Daxxn/LightDrum/Docs/Calculations/PowerConsumption.ods

Sheet: Power Rails
Power Rails
Name | Voltage | Current
+12V | 12 | 0
Vdrive | 12 | 16
VCC | 5 | 0.003
VDD | 3.3 | 0.4421
VAA | 3.3 | 0.014
VDDA | 3.3 | 0
Name | Input | Part # | Output | Current MAX
VCC | 12 | LM22673-5V | 5 | 3
VDD | 5 | AP3401 | 3.3 | 1
VAA | 5 | TPS7A94 | 3.3 | 1
VDDA | 3.3 | Filter | 3.3 | 0.5

Sheet: Consumption
Power Consumption
+12V | Total: | 0 | VCC | Total: | 0.003 | VDD | Total: | 0.4421 | VAA | Total: | 0.014 | VDDA | Total: | 0 | Typical Resistance Draw
Part # | Source | Current | Part # | Source | Current | Part # | Source | Current | Part # | Source | Current | Part # | Source | Current | 20k | 0.000165
 |  |  | SLG55021 | 5 | 0.003 | STM32F412VET3 | 3.3 | 0.16 | PCM1821 | 3.3 | 0.014
 |  |  |  |  |  | PCM1821 | 3.3 | 0.0001
 |  |  |  |  |  | PCA9634 | 3.3 | 0.01
 |  |  |  |  |  | PCA9634 | 3.3 | 0.01
 |  |  |  |  |  | PCA9634 | 3.3 | 0.01
 |  |  |  |  |  | INA4181 A2 | 3.3 | 0.001
 |  |  |  |  |  | INA4181 A2 | 3.3 | 0.001
 |  |  |  |  |  | STR485 | 3.3 | 0.25
