Daxxn/LightDrum/Docs/PowerBudgets/LightDrum REV9 Power Budget.ods

QTY | Light Drum REV9 STM32F412 Loads |  |  | All values are in mA unless otherwise stated.
12V Rail (12V)
QTY | Component | Power Usage
 |  | MIN | AVG | MAX | SUM
2 | ALQ112 | 16.7 | 16.7 | 16.7 | 33.4
8 | LED Strip Channel | -- | 1200 | 1600 | 12800
1 | LED IND | -- | -- | 2 | 2
1 | 5V VCC Rail | -- | -- | 208.297875 | 499.9149
 | Total Load |  | 160.024W | 13335.315mA | 13.3353A
5V Rail (VCC)
 | Component | Power Usage
 |  | MIN | AVG | MAX
1 | LTC2877-Driver | 0.025 | 1.1 | 1.2 | 1.2
2 | R/A IND LEDs | -- | -- | 1.2 | 2.4
1 | NX4024T032 | -- | 85 | 120 | 120
5 | LED IND | -- | -- | 2 | 10
1 | 74AUP2G04 | -- | 0.0005 | 0.0009 | 0.0009
1 | PC817 | -- | 17 | 17 | 17
1 | 3.3V VDD Rail | -- | -- | 216.225 | 344.374
1 | 3.3V VDDA Rail | -- | -- | 3.2604 | 4.94
 | Total Load |  | 2.5W | 499.915mA | 0.4999A
3.3V Rail (VDD)
QTY | Component | Power Usage
 |  | MIN | AVG | MAX | SUM
1 | STM32F446ZCH6 | 50 | 150 | 240 | 240
1 | 74HC2G08 | -- | 1 | 50 | 50
1 | 24LC04 | 0.001 | 1 | 3 | 3
1 | AZV321 | -- | 0.08 | 0.27 | 0.27
2 | 30K Pots | -- | -- | 0.109 | 0.218
1 | HP Switch | -- | -- | 0.326 | 0.326
3 | PCA9634 | -- | 2.5 | 10 | 30
2 | INA4181A2 | -- | 0.69 | 0.9 | 1.8
1 | LED IND | -- | -- | 2 | 2
1 | TPL0401 | 0.0015 | -- | 5 | 5
1 | STP16CP05 | 4 | 4.5 | 11.7 | 11.7
1 | LTC2877-Logic | 0.025 | 0.12 | 0.06 | 0.06
 | Total Load |  | 1.136W | 344.374mA | 0.3444A
3.3V Analog Rail (VDDA)
 | Component | Power Usage
 |  | MIN | AVG | MAX | SUM
2 | MCP3561 | -- | 1.65 | 2.2 | 4.4
2 | AZV321 | -- | 0.08 | 0.27 | 0.54
 | Total Load |  | .016W | 4.94mA | 0.0049A
Light Drum REV9 STM32F412 Power Supplies
Rail | Component | NOM | MAX | VOLTAGE
3.3V | AP3401 | 1 | 1.3 | 3.3
3.3VA | TPS7A94 | 0.75 | 1 | 3.3
5V | LM22673-ADJ | 3 | 4.2 | 5
12V | External Power Brick | 12.5 | 14 | 12
