Daxxn/LightDrum/Docs/Renders/REV7/test.pdf

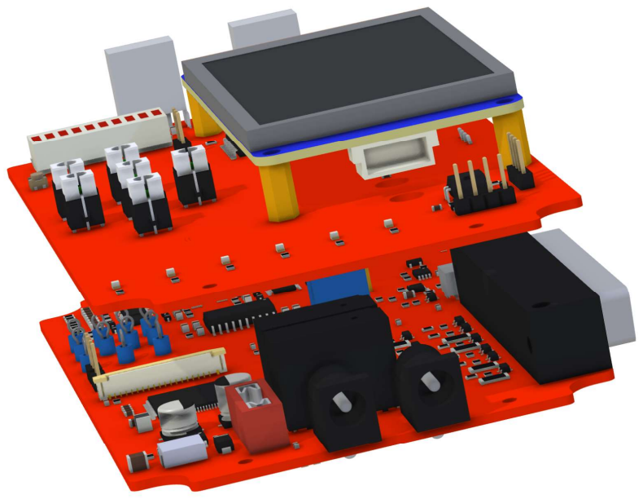
[picture p7: figure]
