Daxxn/LightDrum/Docs/Schematics/REV9/LightDrum-Main-REV9-SCH.pdf

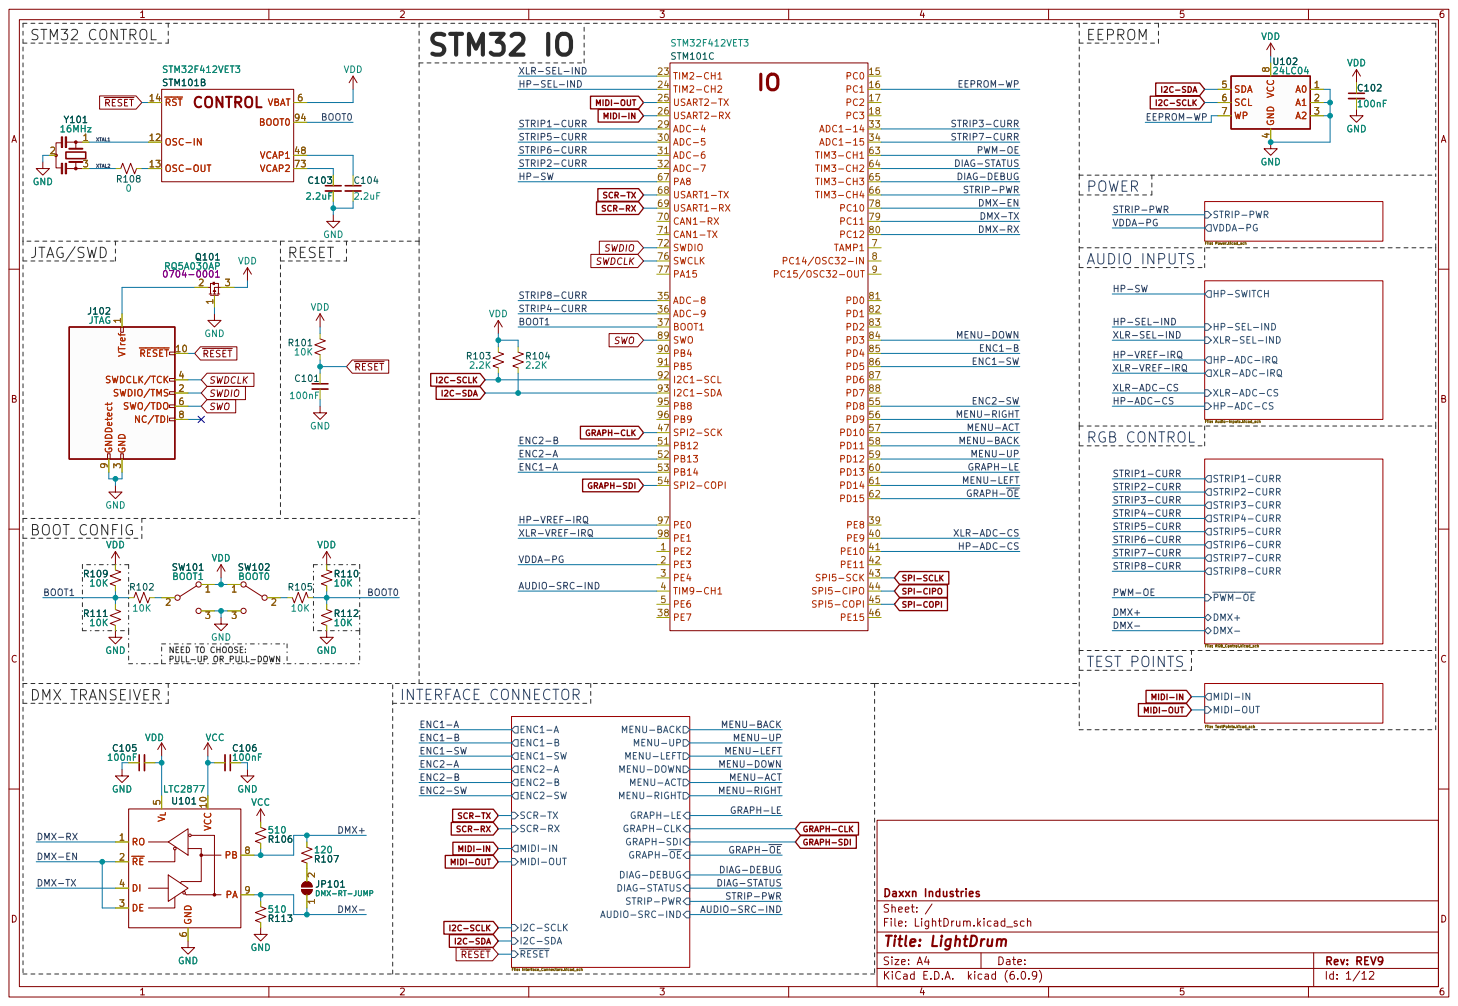
[picture p81: page 1]

STM32F412VET3 GND
NEED TO CHOOSE: PULL-UP OR PULL-DOWN GND

4 SDA 5 SCL 6 WP 7 VCC

MIDI-IN
SCR-TX GRAPH-CLK
SCR-RX

VDDA-PG POWER
File: Power.kicad_sch STRIP1-CURR
File: TestPoints.kicad_sch HP-SWITCH

JTAG/SWD | | 2 3 | RESET

HP-ADC-IRQ AUDIO INPUTS

HP-VREF-IRQ MENU-DOWN

3 SWDCLK/TCK 4 SWO/TDO 6 NC/TDI 8 GNDDetect 9

3 SWDCLK/TCK 4 SWO/TDO 6 NC/TDI 8 GNDDetect 9 VDD GND

XLR-ADC-IRQ
XLR-ADC-CS HP-ADC-CS

File: Audio-Inputs.kicad_sch MIDI-OUT MIDI-IN
ENC2-B
ENC2-A

~{PWM-OE} DMX- DMX+ RGB CONTROL

SPI-SCLK
SPI-COPI SPI-CIPO

AUDIO-SRC-IND GRAPH-~{OE} GRAPH-SDI GRAPH-CLK MENU-UP MENU-ACT MENU-LEFT MENU-BACK MENU-DOWN MENU-RIGHT SCR-TX

MENU-ACT MENU-UP MENU-DOWN MENU-LEFT DMX-RX DMX-TX DMX-EN

STRIP-PWR GRAPH-LE DIAG-STATUS

DIAG-STATUS GRAPH-~{OE} DIAG-DEBUG

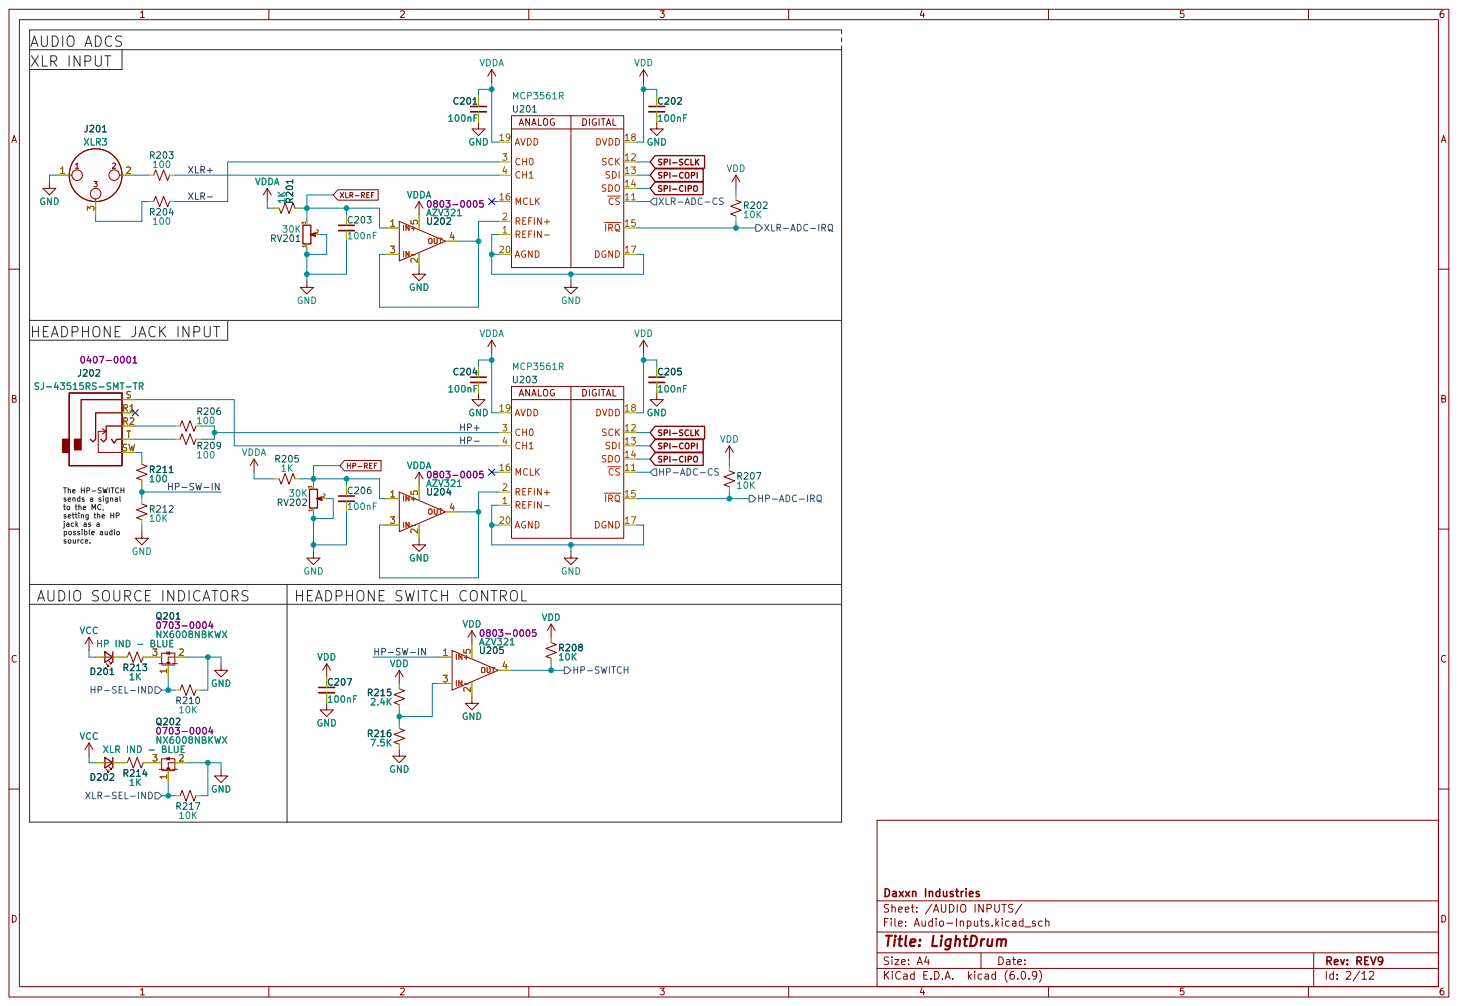
[picture p82: page 2]

HP- AUDIO ADCS
XLR INPUT
100 VCC
XLR-ADC-CS HP-ADC-CS HP-SWITCH

The HP-SWITCH
sends a signal to the MC, setting the HP

File: Audio-Inputs.kicad_sch Sheet: /AUDIO INPUTS/ Daxxn Industries

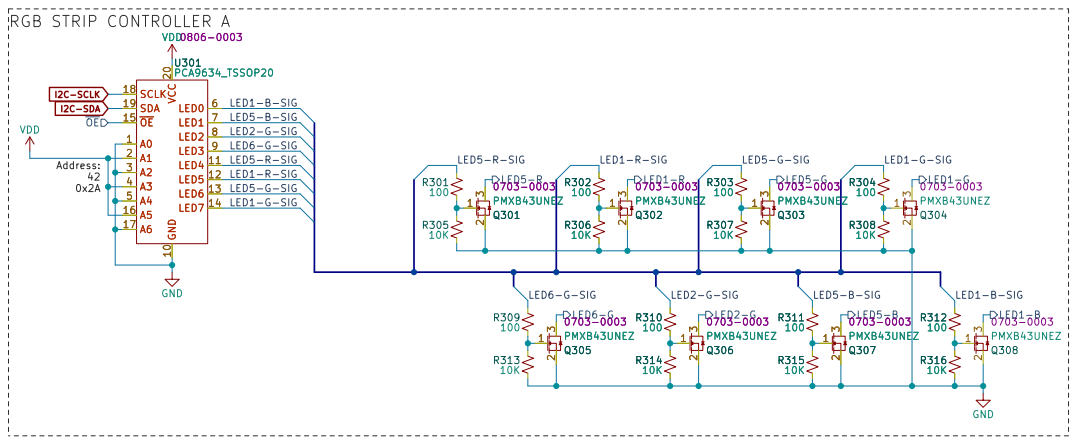
[picture p83: page 3]

LED6-G-SIG RGB STRIP CONTROLLER A
0806-0003 GND

File: RGB_Control-1.kicad_sch Sheet: /RGB CONTROL/RGB Control 1/ Daxxn Industries

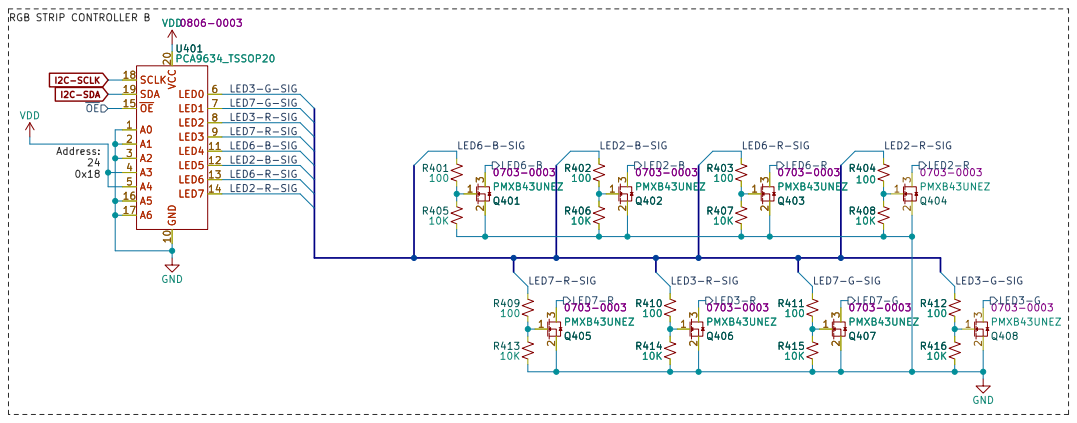
[picture p84: page 4]

File: RGB_Control-2.kicad_sch Sheet: /RGB CONTROL/RGB Control 2/ Daxxn Industries

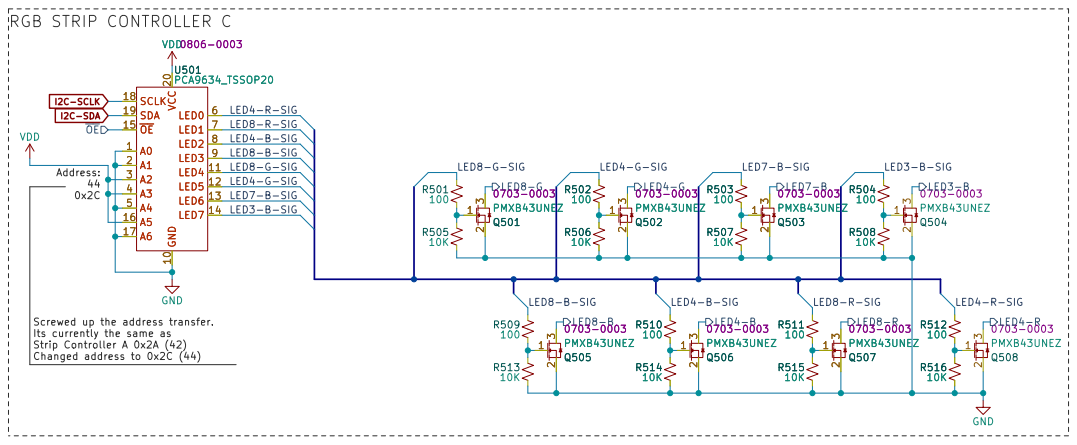
[picture p85: page 5]

Screwed up the address transfer.
Its currently the same as
Strip Controller A 0x2A (42)
Changed address to 0x2C (44)

File: RGB_Control-3.kicad_sch Sheet: /RGB CONTROL/RGB Control 3/ Daxxn Industries

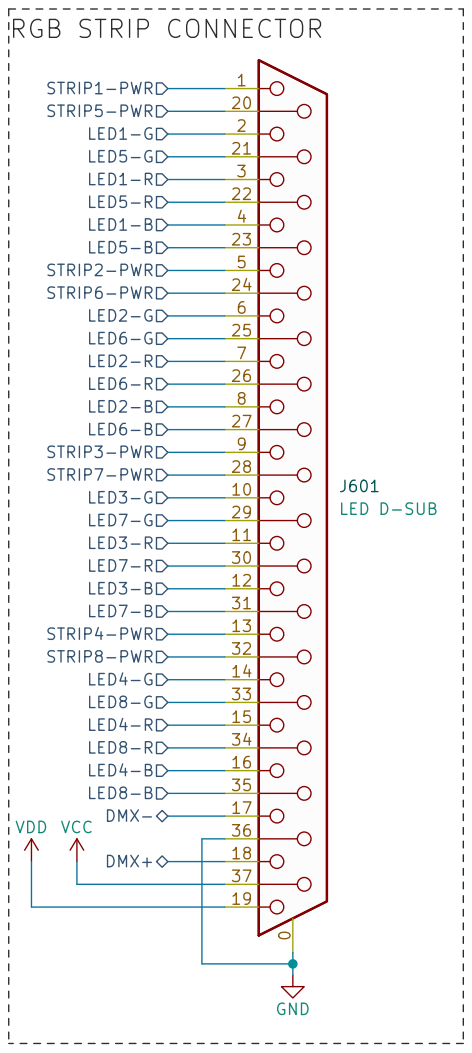
[picture p86: page 6]

DMX- RGB STRIP CONNECTOR

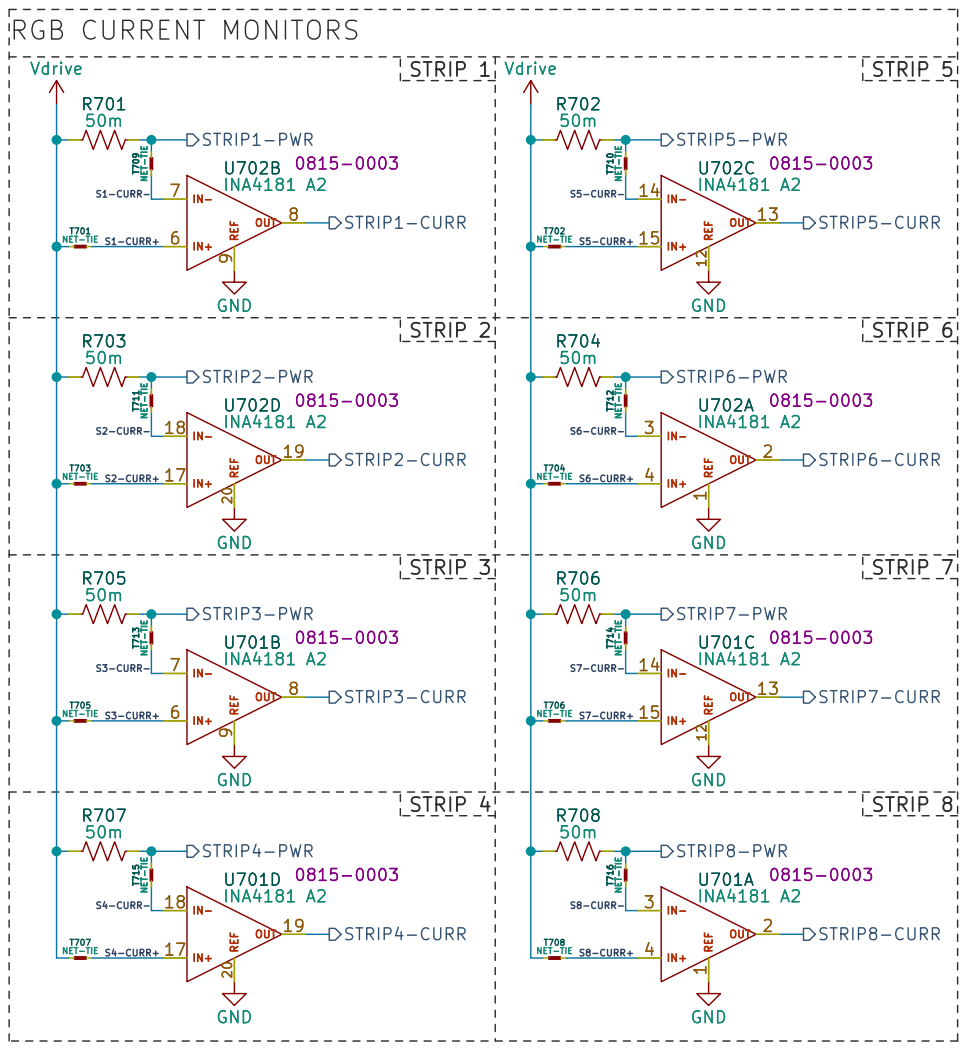
[picture p87: page 7]

T703 NET-TIE | GND STRIP2-PWR 0815-0003 0815-0003 U702D OUT 19 REF 20 U702D OUT 19 REF 20 R705 IN+ 17 IN+ 17 | T704 NET-TIER704 50m 50m 50m T712 NET-TIE T706 NET-TIE T713 NET-TIE | IN+ 15 T714 NET-TIE T716 NET-TIE Vdrive R701 STRIP6-PWR GND T712 NET-TIE R708 GND 0815-0003 0815-0003 REF 1 IN+ 4 U702A OUT 2 OUT 2 REF 1 IN+ 4 R706

50m 50m T705 NET-TIE | OUT 19 REF 20 STRIP3-PWR 0815-0003 U701B OUT 8 REF 9 U701B IN+ 6 IN+ 6 | 50m | U702A STRIP7-PWR OUT 13 0815-0003 REF 12 IN+ 15 U701C U701C

GND

Sheet: /RGB CONTROL/Strip Current Monitors/ Daxxn Industries

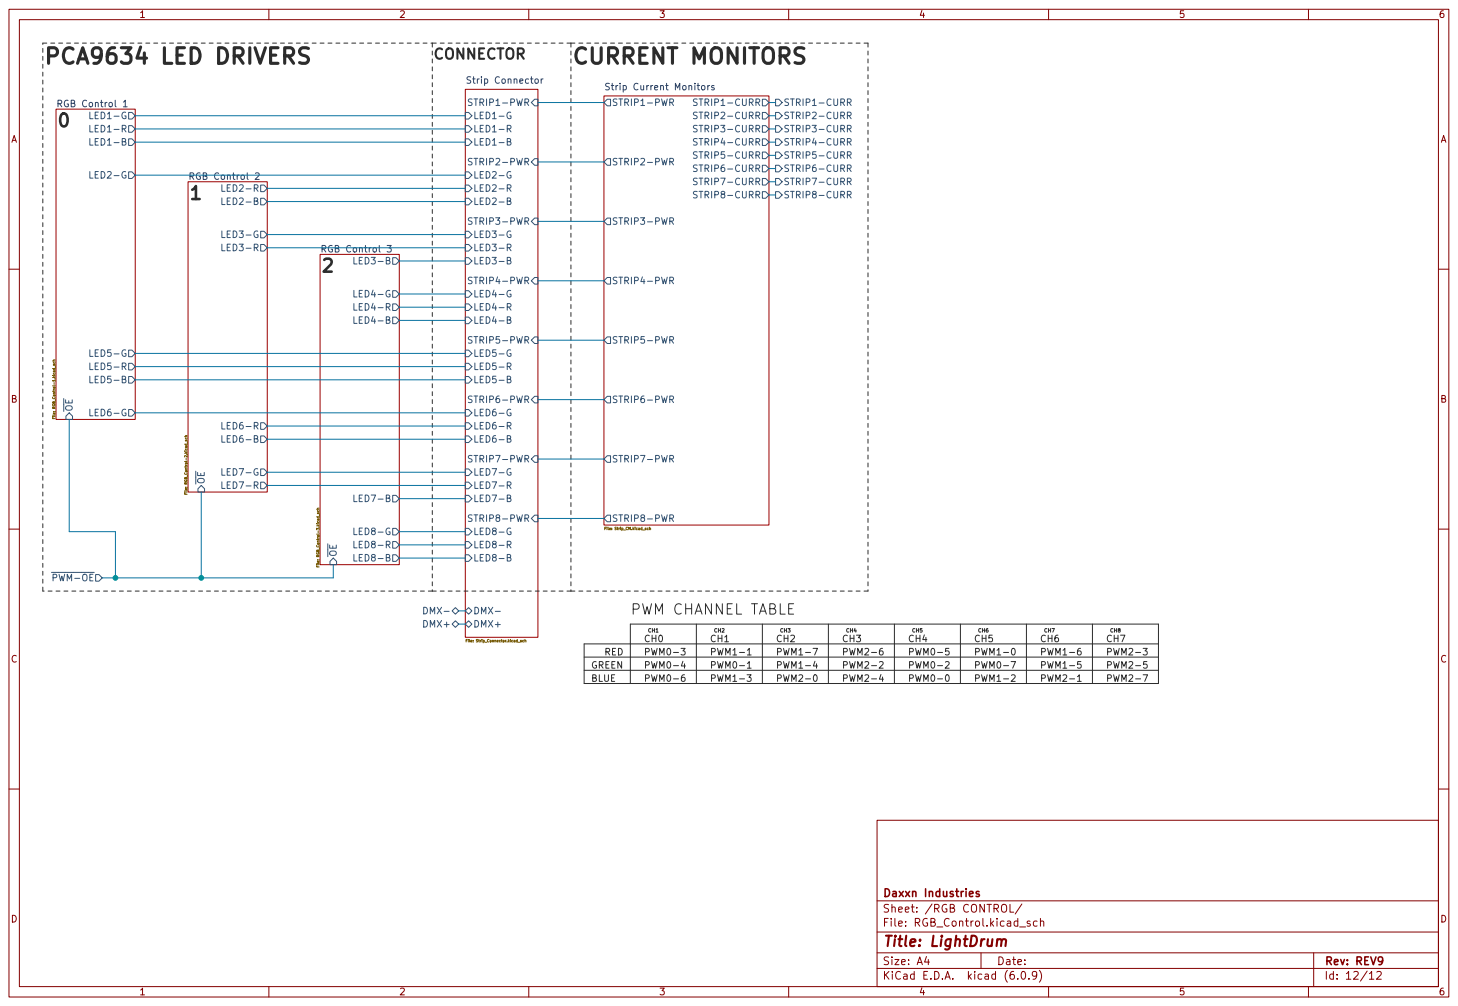
[picture p88: page 8]

PWM1-6 PCA9634 LED DRIVERS
LED2-G ~{OE} RGB Control 1 File: RGB_Control-1.kicad_sch

LED6-R LED6-B LED7-G LED7-R

LED7-B LED8-G LED8-R

PWM0-3 PWM0-4 CH1 | CH2 | CH3 RED | CH3 CH4 CH2 | CH4 PWM CHANNEL TABLE | PWM1-0 BLUE GREEN

PWM0-6 | CH1 | | | CH5 | CH5 PWM2-4 PWM2-6 CH0

PWM0-0

File: RGB_Control.kicad_sch Sheet: /RGB CONTROL/ Daxxn Industries

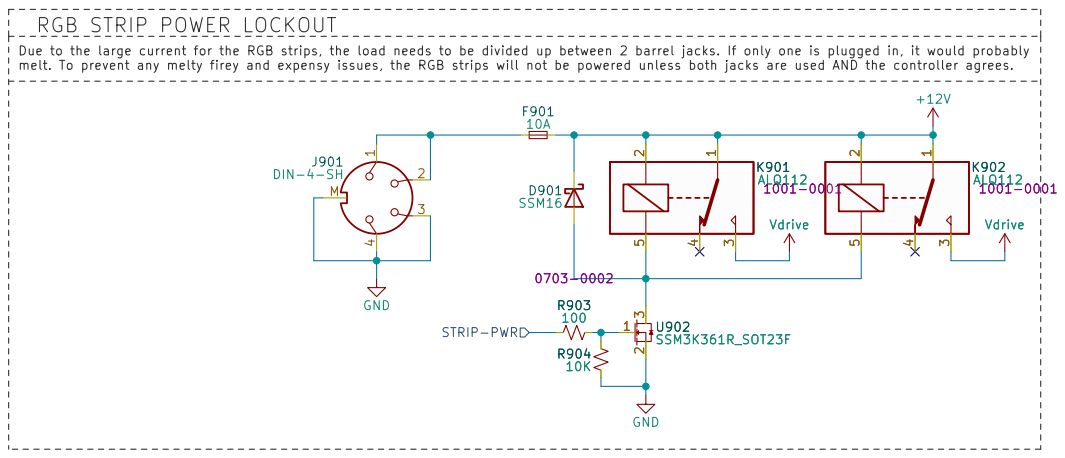
[picture p89: page 9]

RGB STRIP POWER LOCKOUT

Due to the large current for the RGB strips, the load needs to be divided up between 2 barrel jacks. If only one is plugged in, it would probably
melt. To prevent any melty firey and expensy issues, the RGB strips will not be powered unless both jacks are used AND the controller agrees.

Sheet: /POWER/LED_Power_Control/ Daxxn Industries

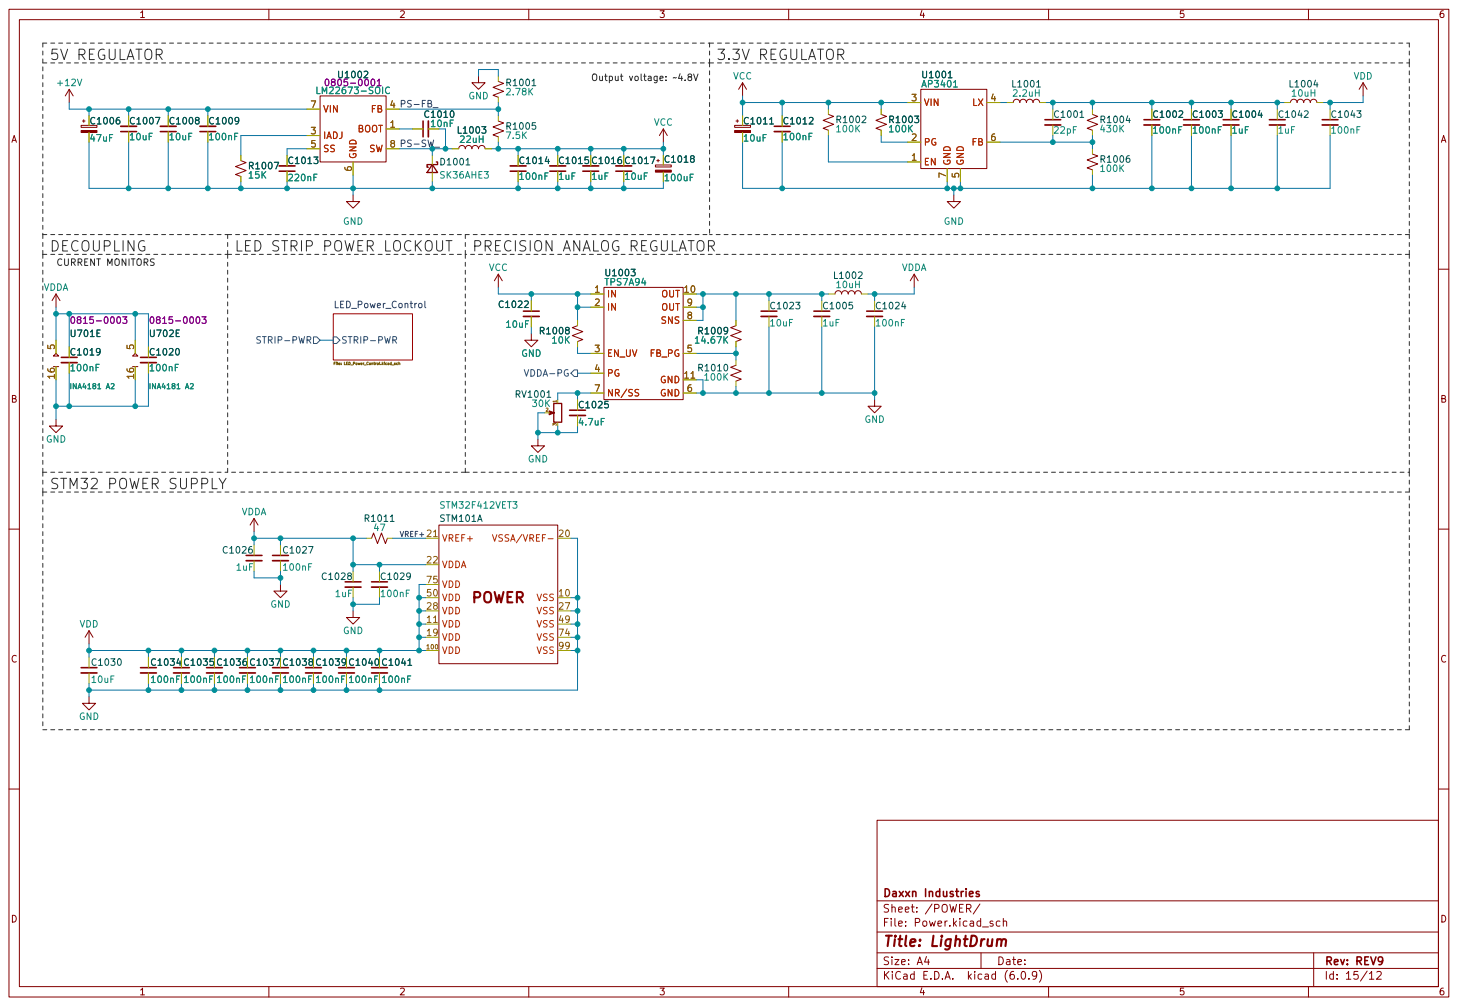
[picture p90: page 10]

5V REGULATOR | | 3.3V REGULATOR

Output voltage: ~4.8V R1001 | | VCC VDD

EN 1 PG 2 VIN 3

CURRENT MONITORS STM32 POWER SUPPLY

File: Power.kicad_sch Sheet: /POWER/ Daxxn Industries

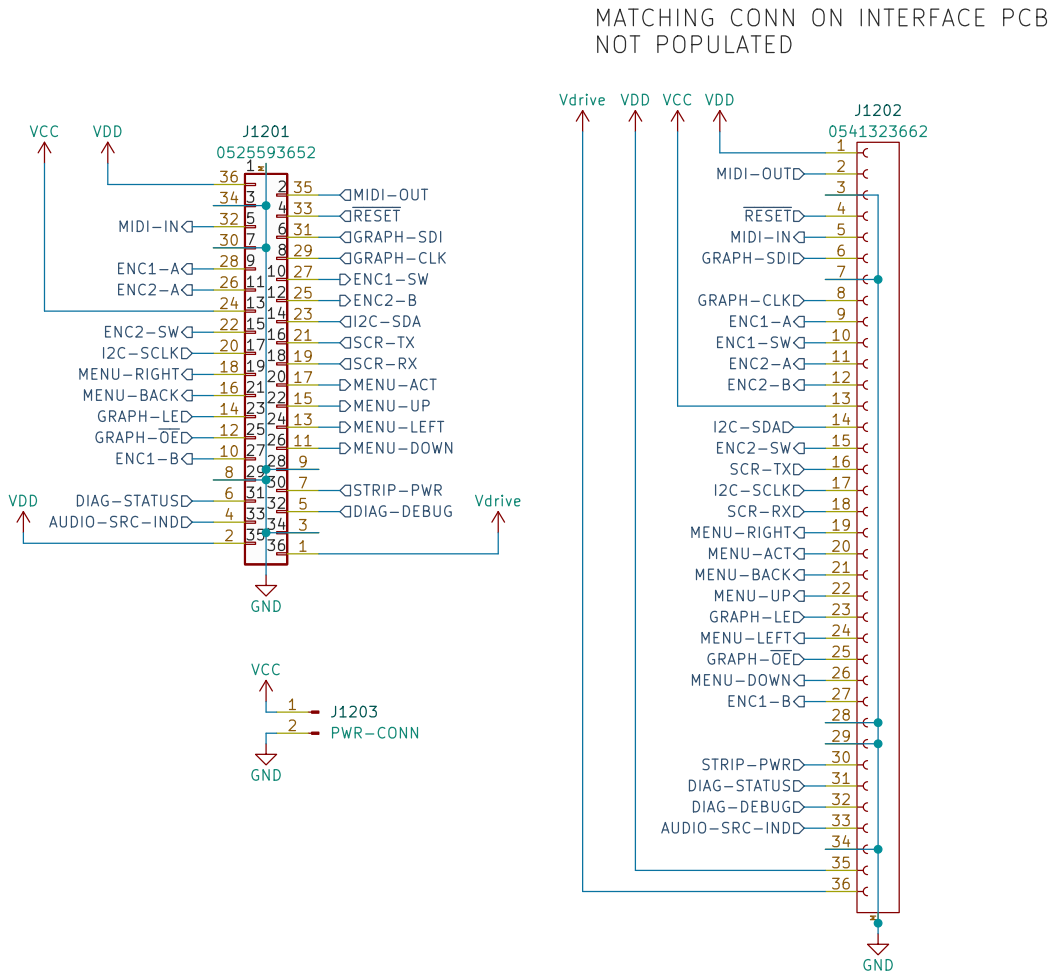
[picture p91: page 11]

NOT POPULATED
~{RESET} MENU-BACK MENU-UP GRAPH-LE MENU-LEFT SCR-TX

MIDI-OUT MIDI-IN

ENC1-B GRAPH-~{OE} ENC2-SW
I2C-SCLK MENU-RIGHT MENU-BACK GRAPH-LE

SCR-RX MENU-ACT

AUDIO-SRC-IND GRAPH-~{OE}

File: Interface_Connectors.kicad_sch Sheet: /INTERFACE CONNECTOR/ Daxxn Industries

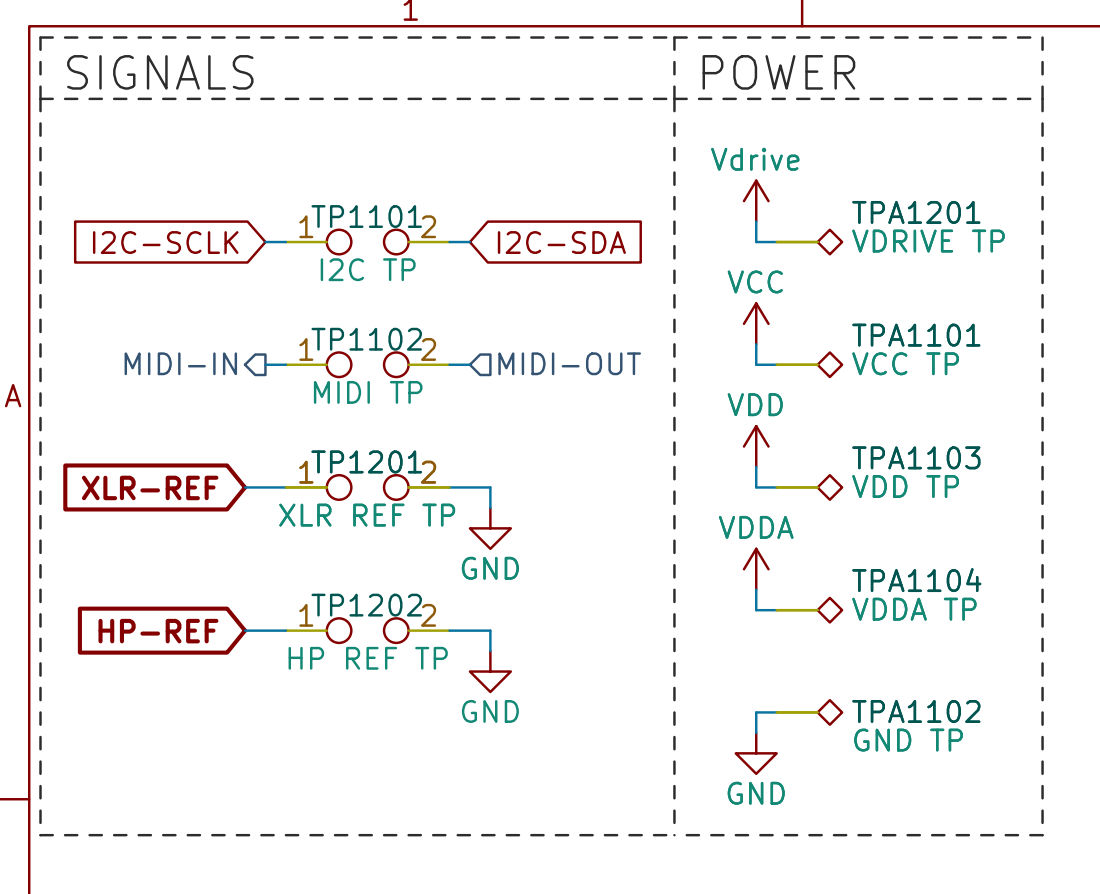
[picture p92: page 12]

File: TestPoints.kicad_sch Sheet: /TEST POINTS/ Daxxn Industries
