Daxxn/LightDrum/Docs/Schematics/PreviousRevisions/REV4/SpectrumFilterDTR-REV2-SCH.pdf

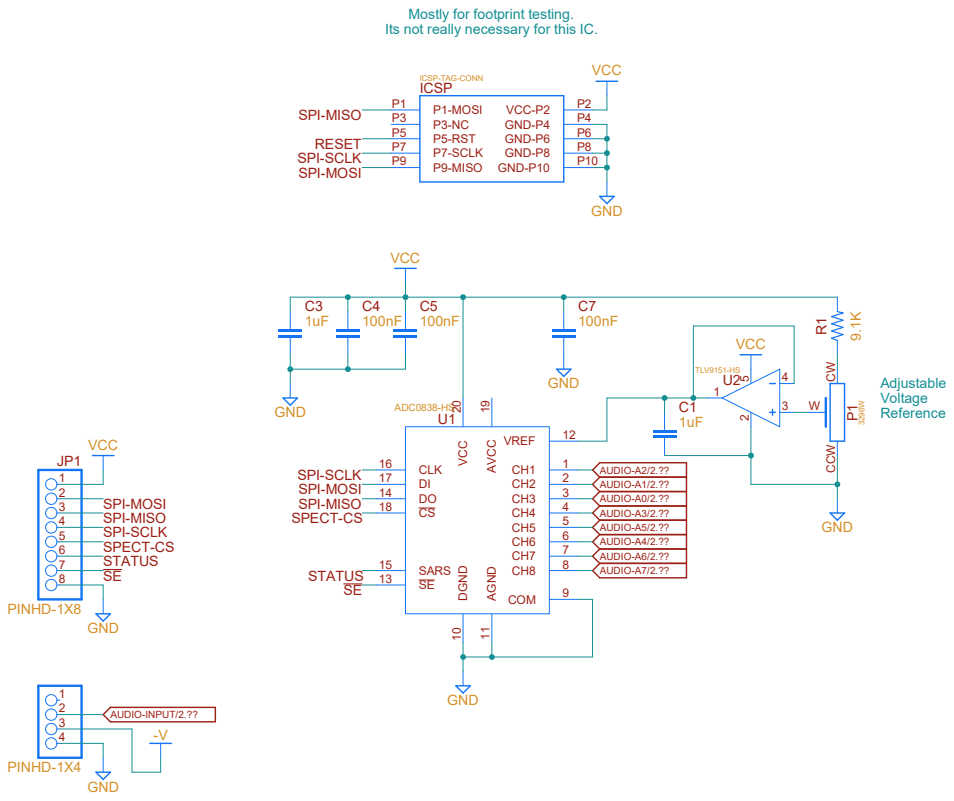
[picture p93: page 1]

Mostly for footprint testing.
Its not really necessary for this IC.

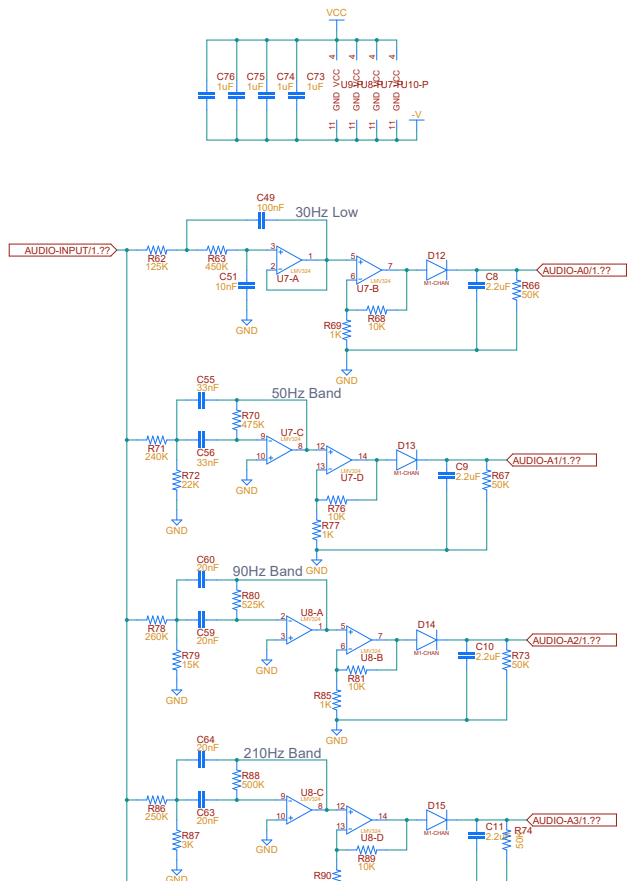
[picture p94: page 2]

## 750Hz Band

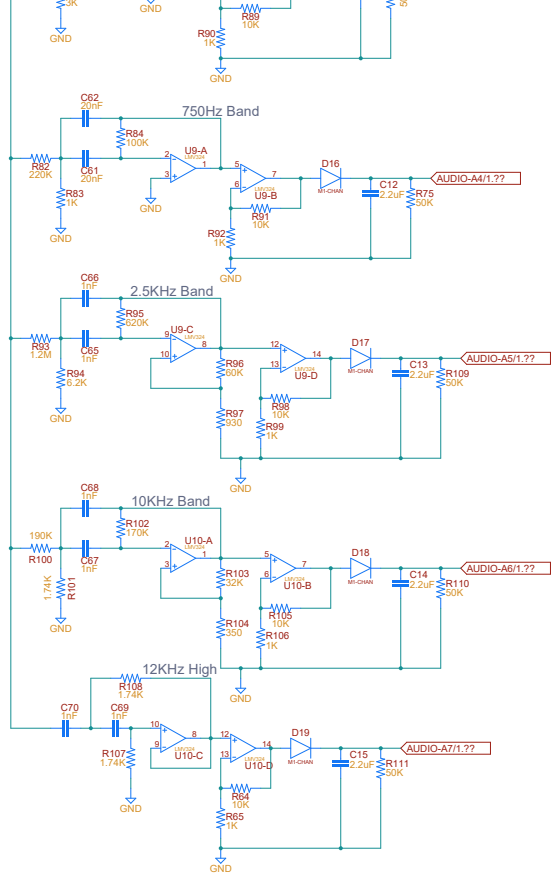
[picture p95: page 3]
