Daxxn/LightDrum/Docs/Schematics/REV9/LightDrum-Interface-REV6-COMP-BOT.pdf

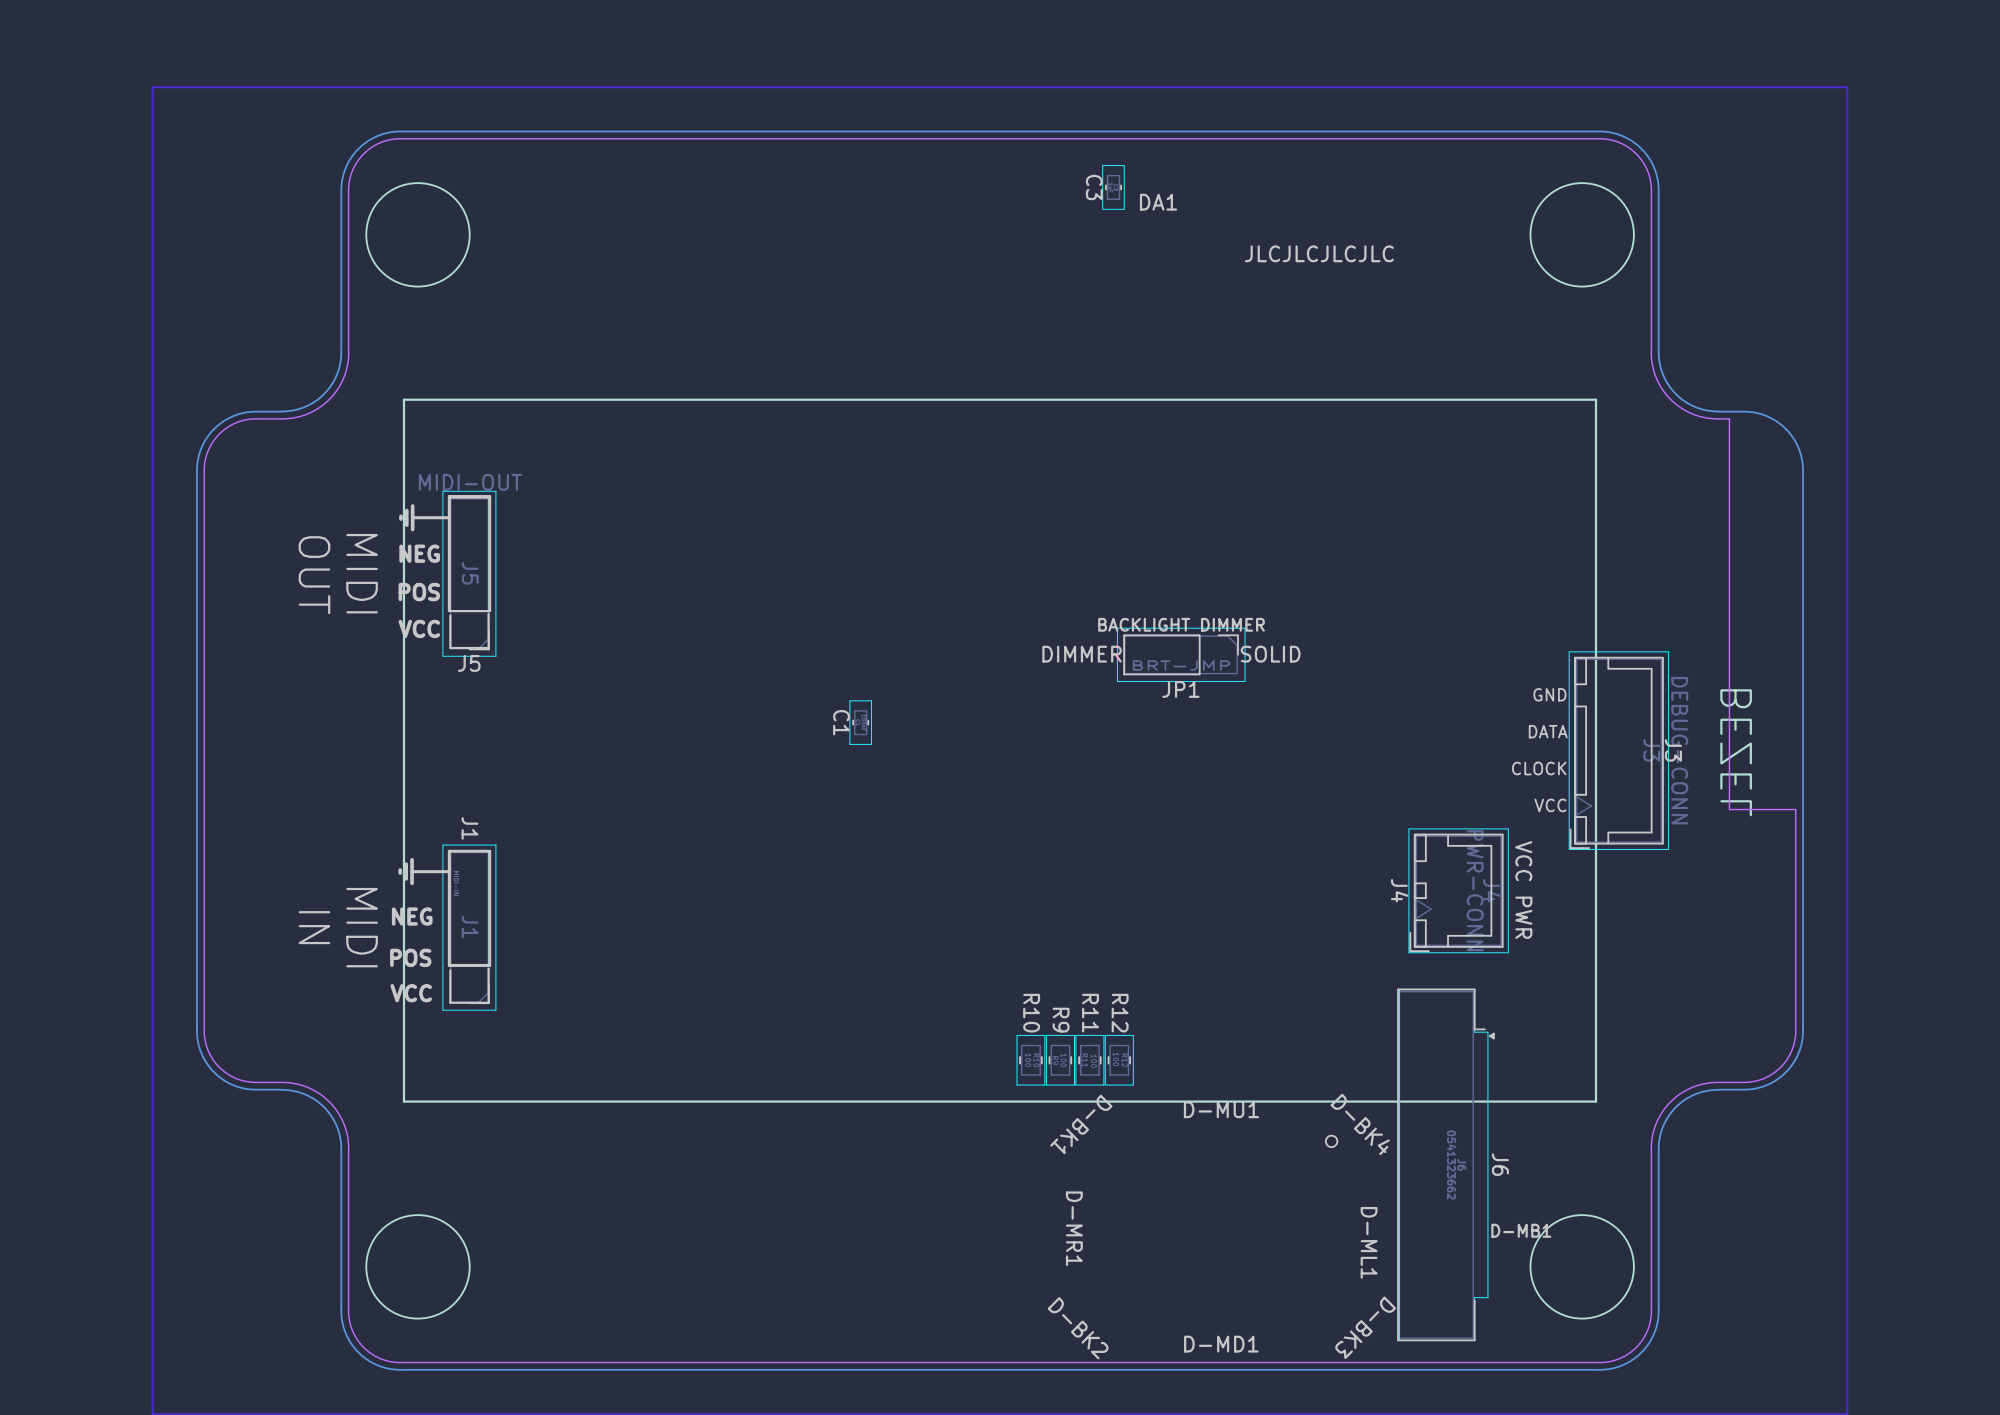
[picture p113: page 1]
