Daxxn/LightDrum/Docs/Schematics/REV9/LightDrum-Interface-REV6-COMP-TOP.pdf

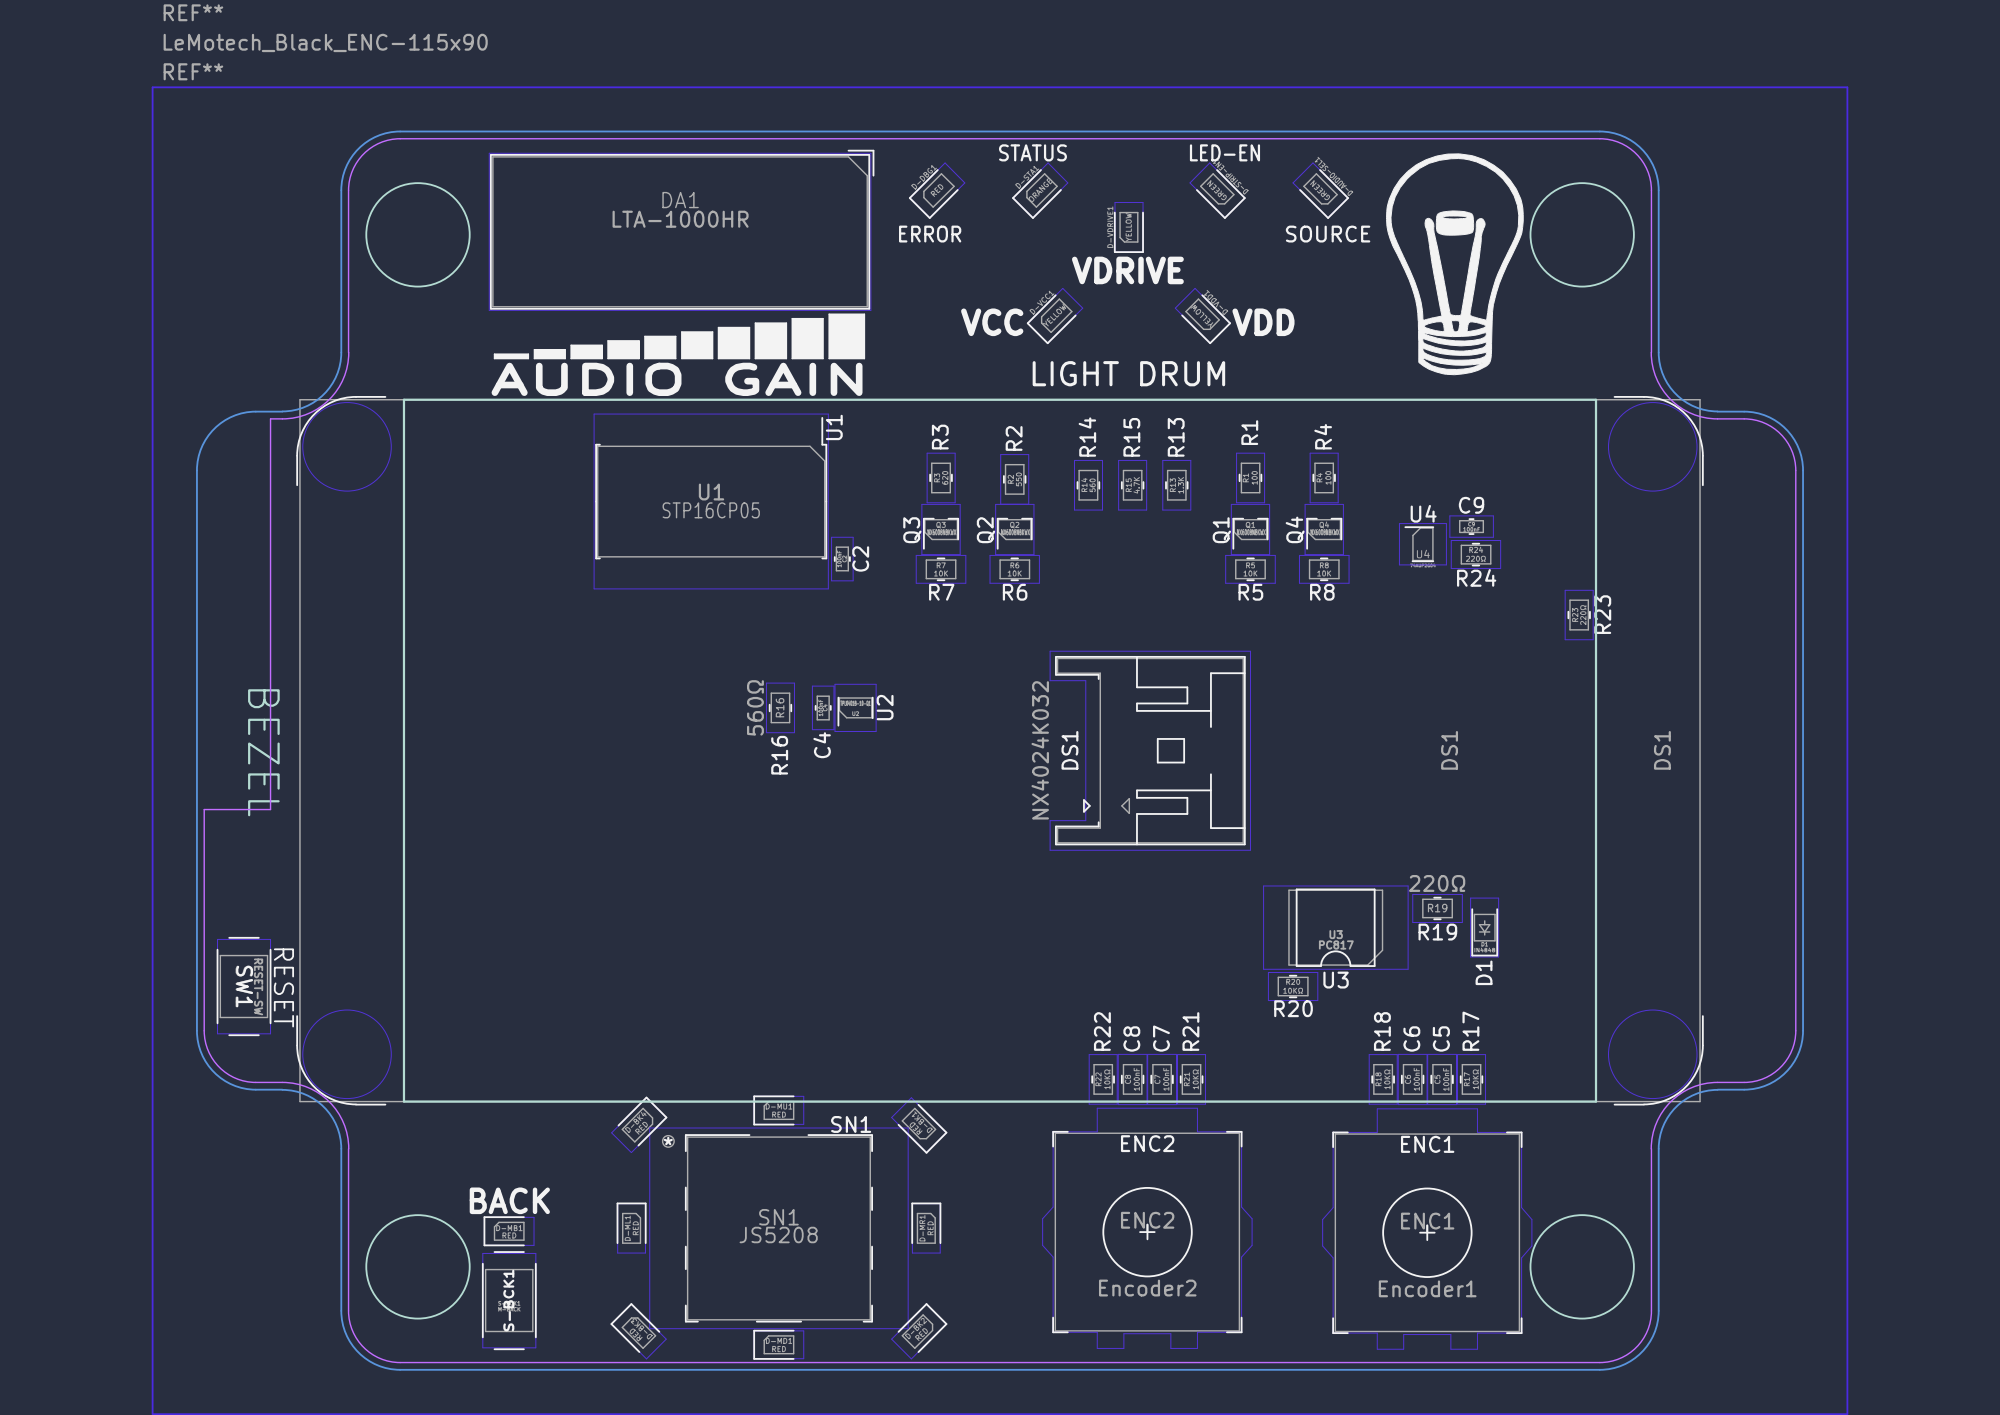
[picture p114: page 1]
