Daxxn/LightDrum/Docs/Schematics/REV9/LightDrum-Main-REV9-COMP-BOT.pdf

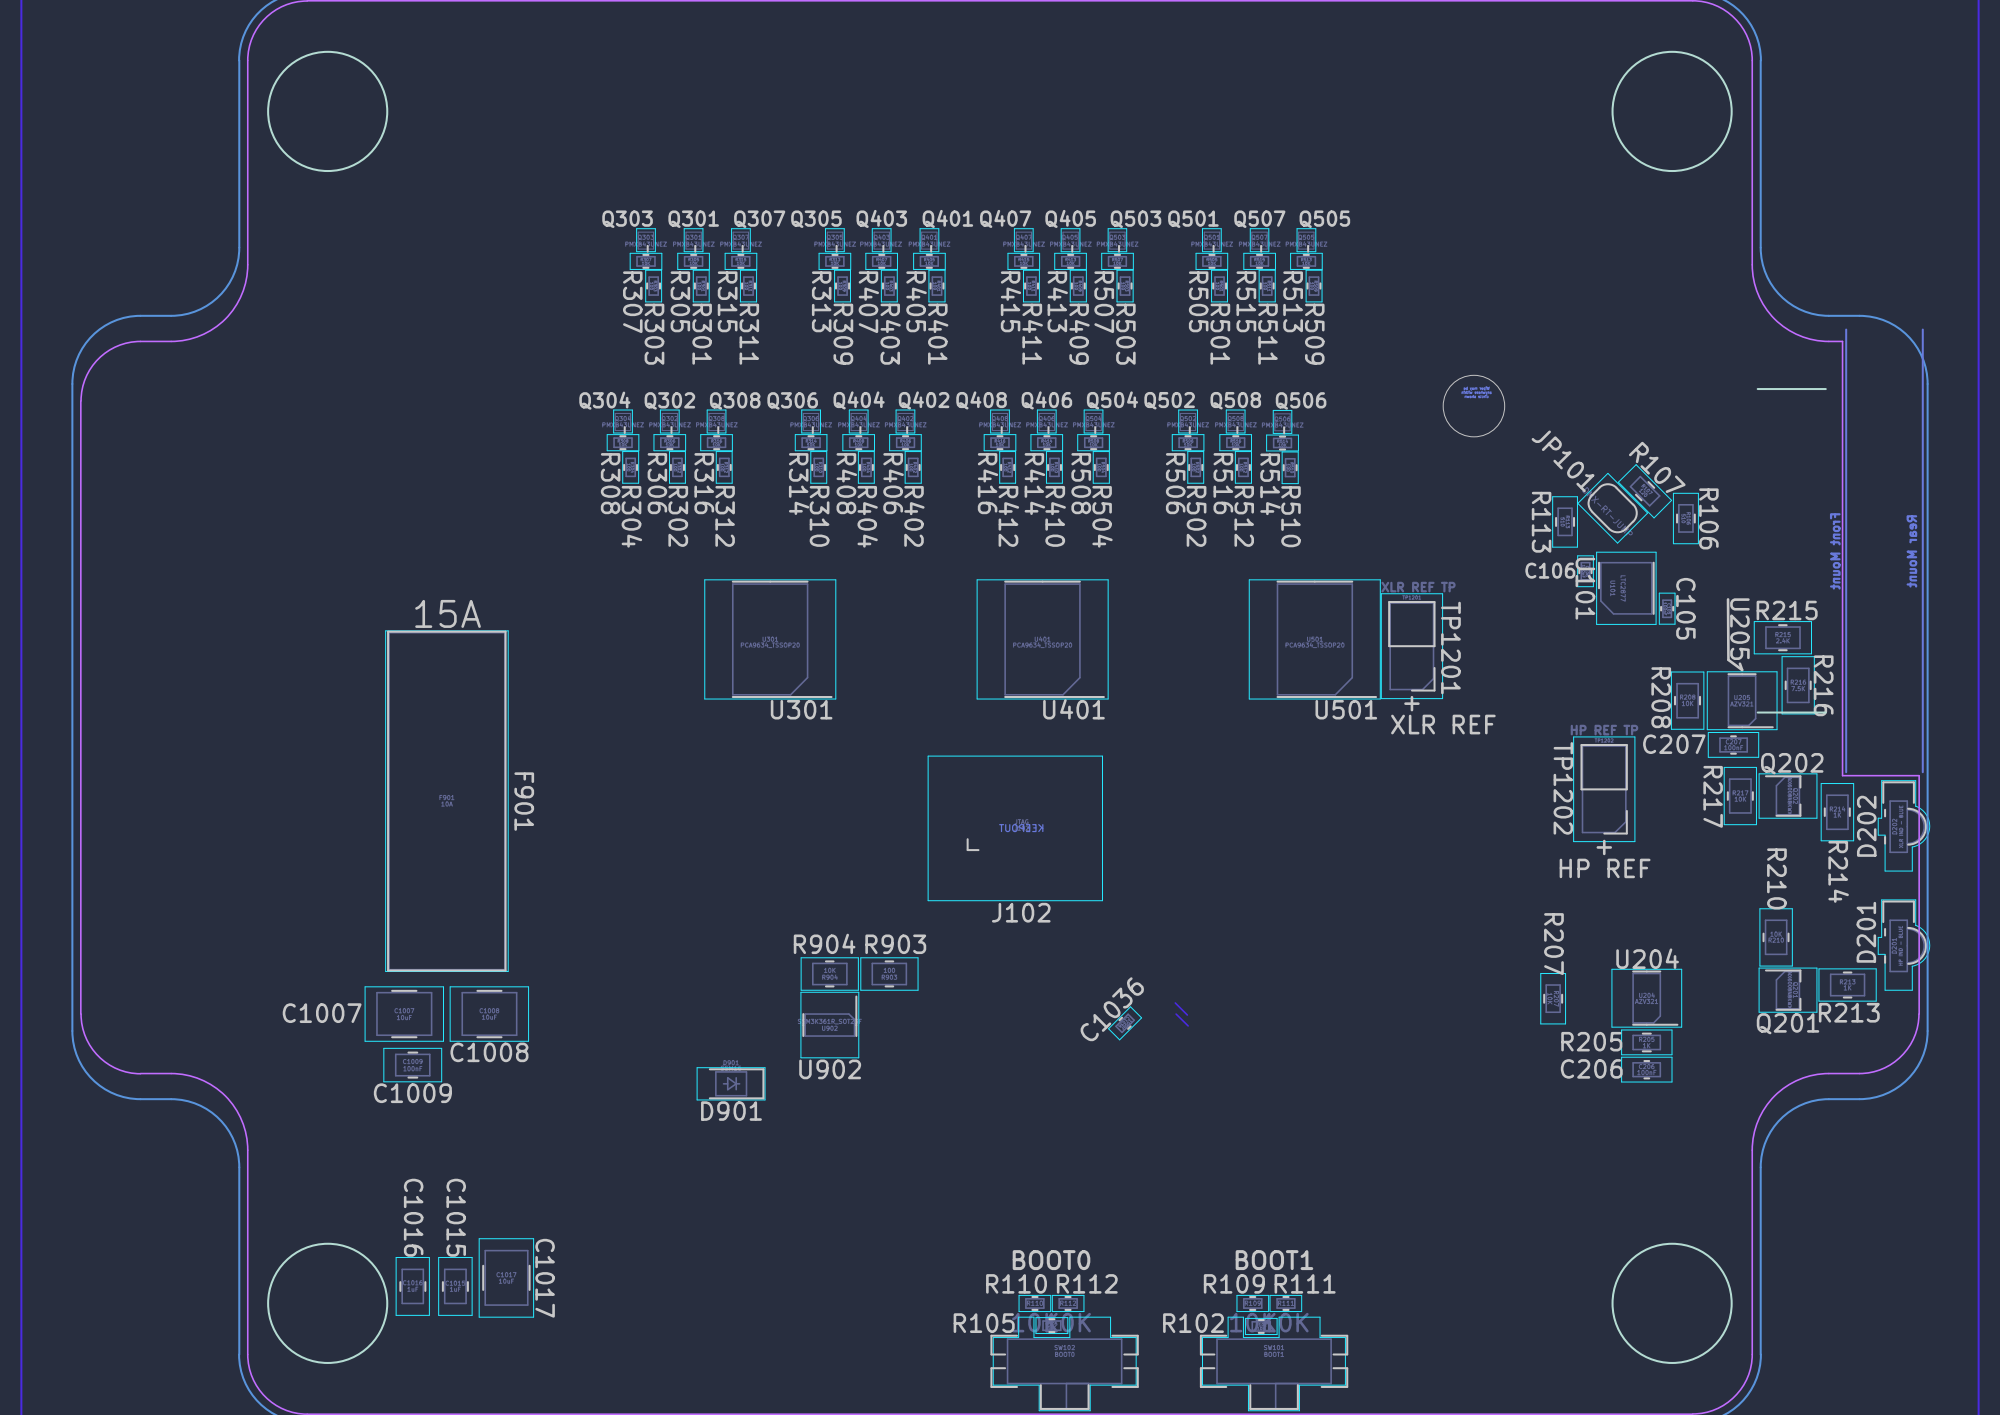
[picture p115: page 1]
