Daxxn/LightDrum/Docs/Schematics/REV9/LightDrum-Main-REV9-COMP-TOP.pdf

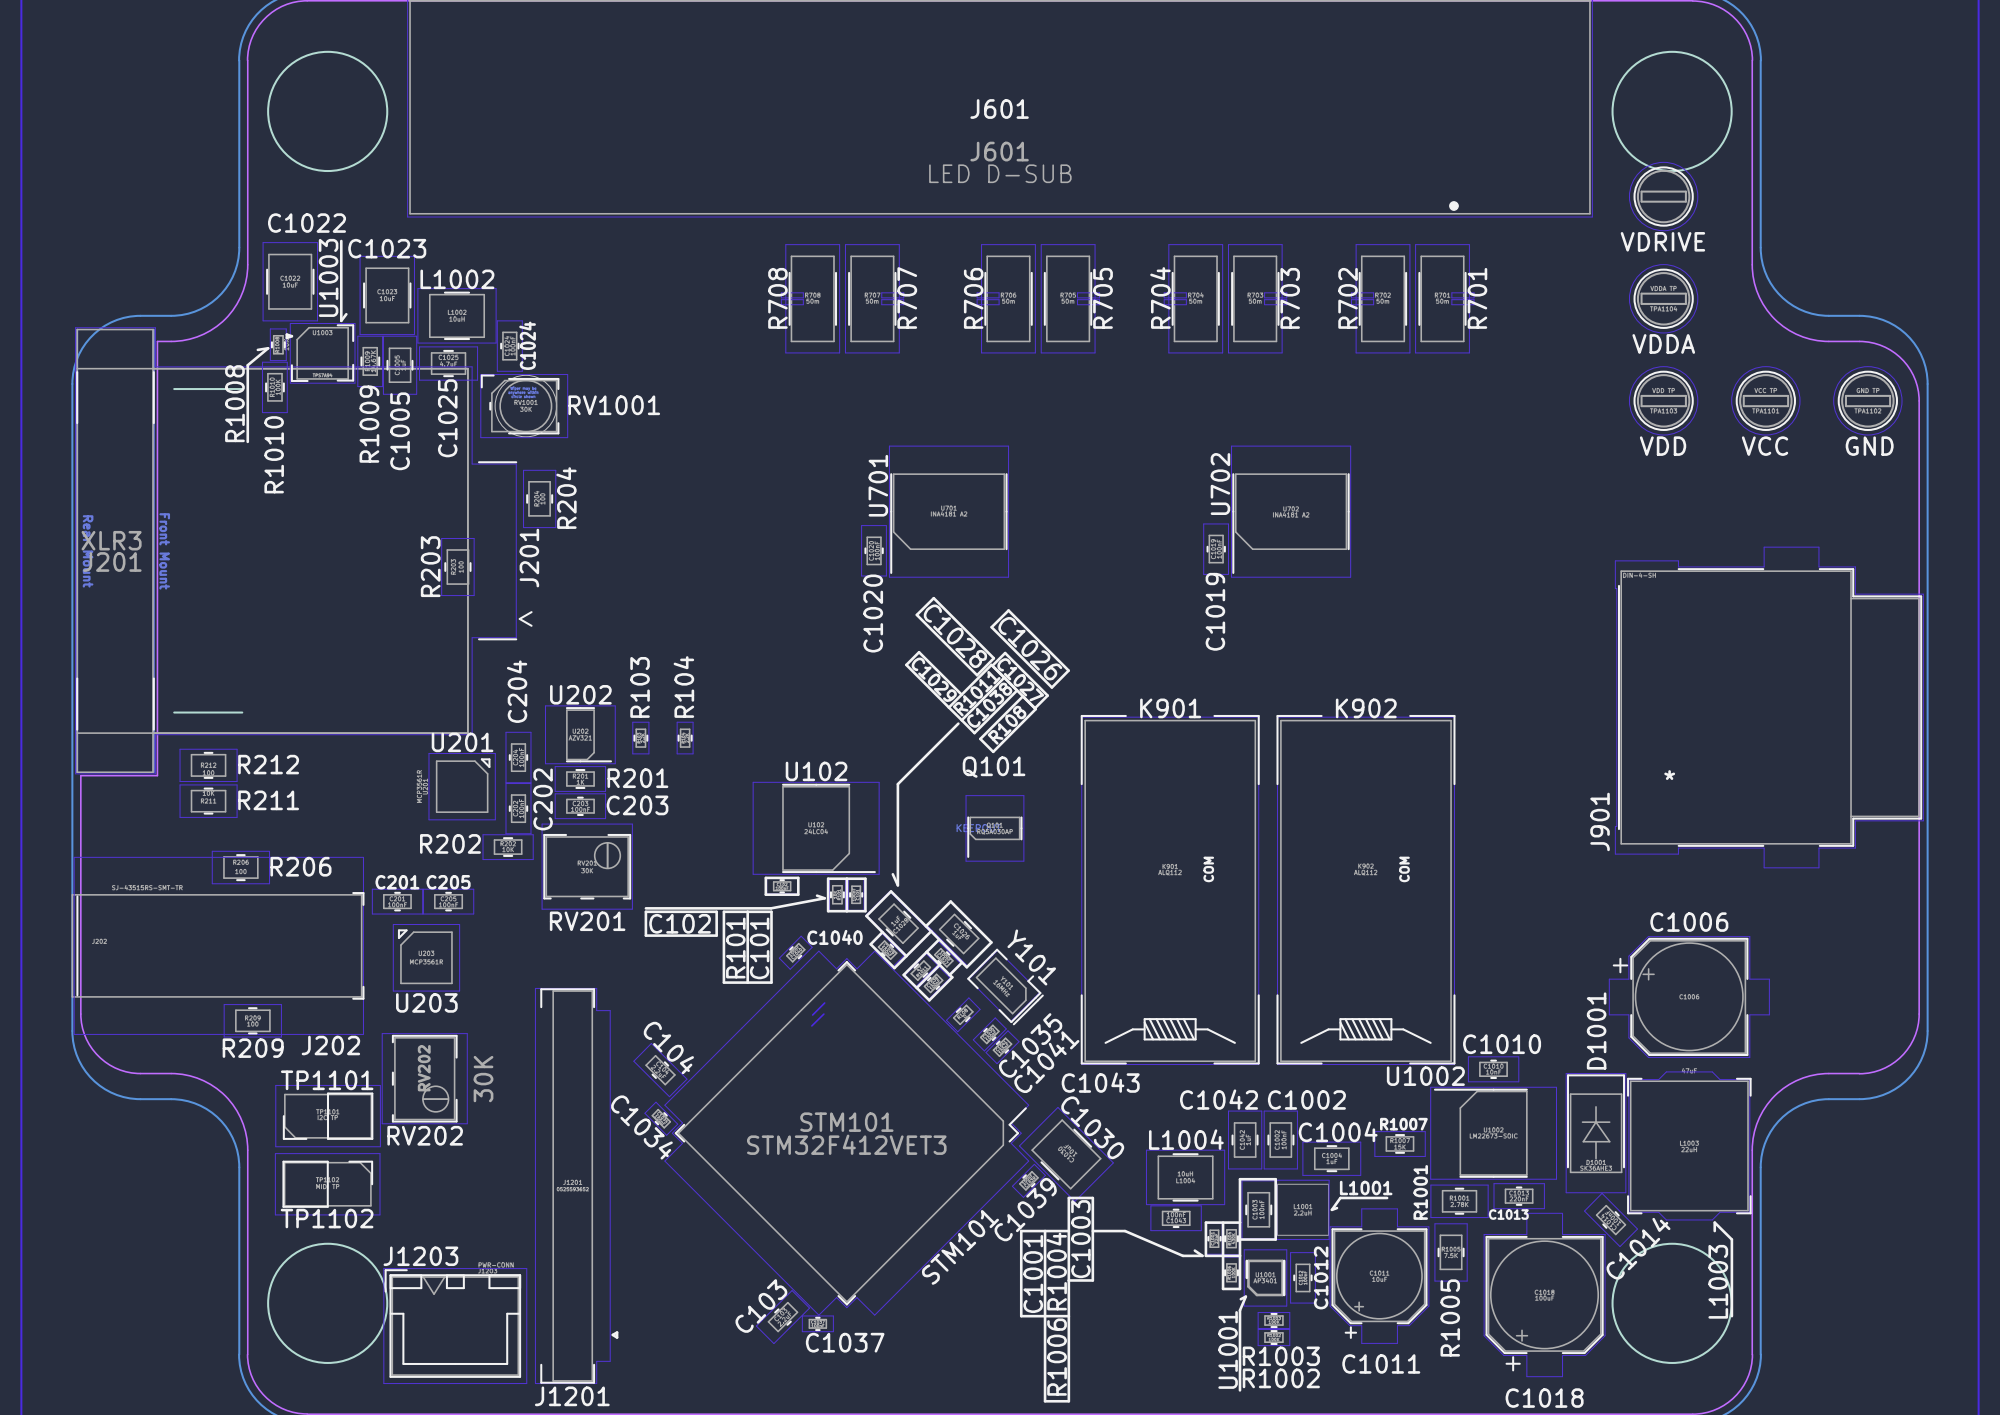
[picture p116: page 1]
