Daxxn/LightDrum/Docs/Schematics/REV7/Light-Drum-Interface-REV3-Comp-Top.pdf

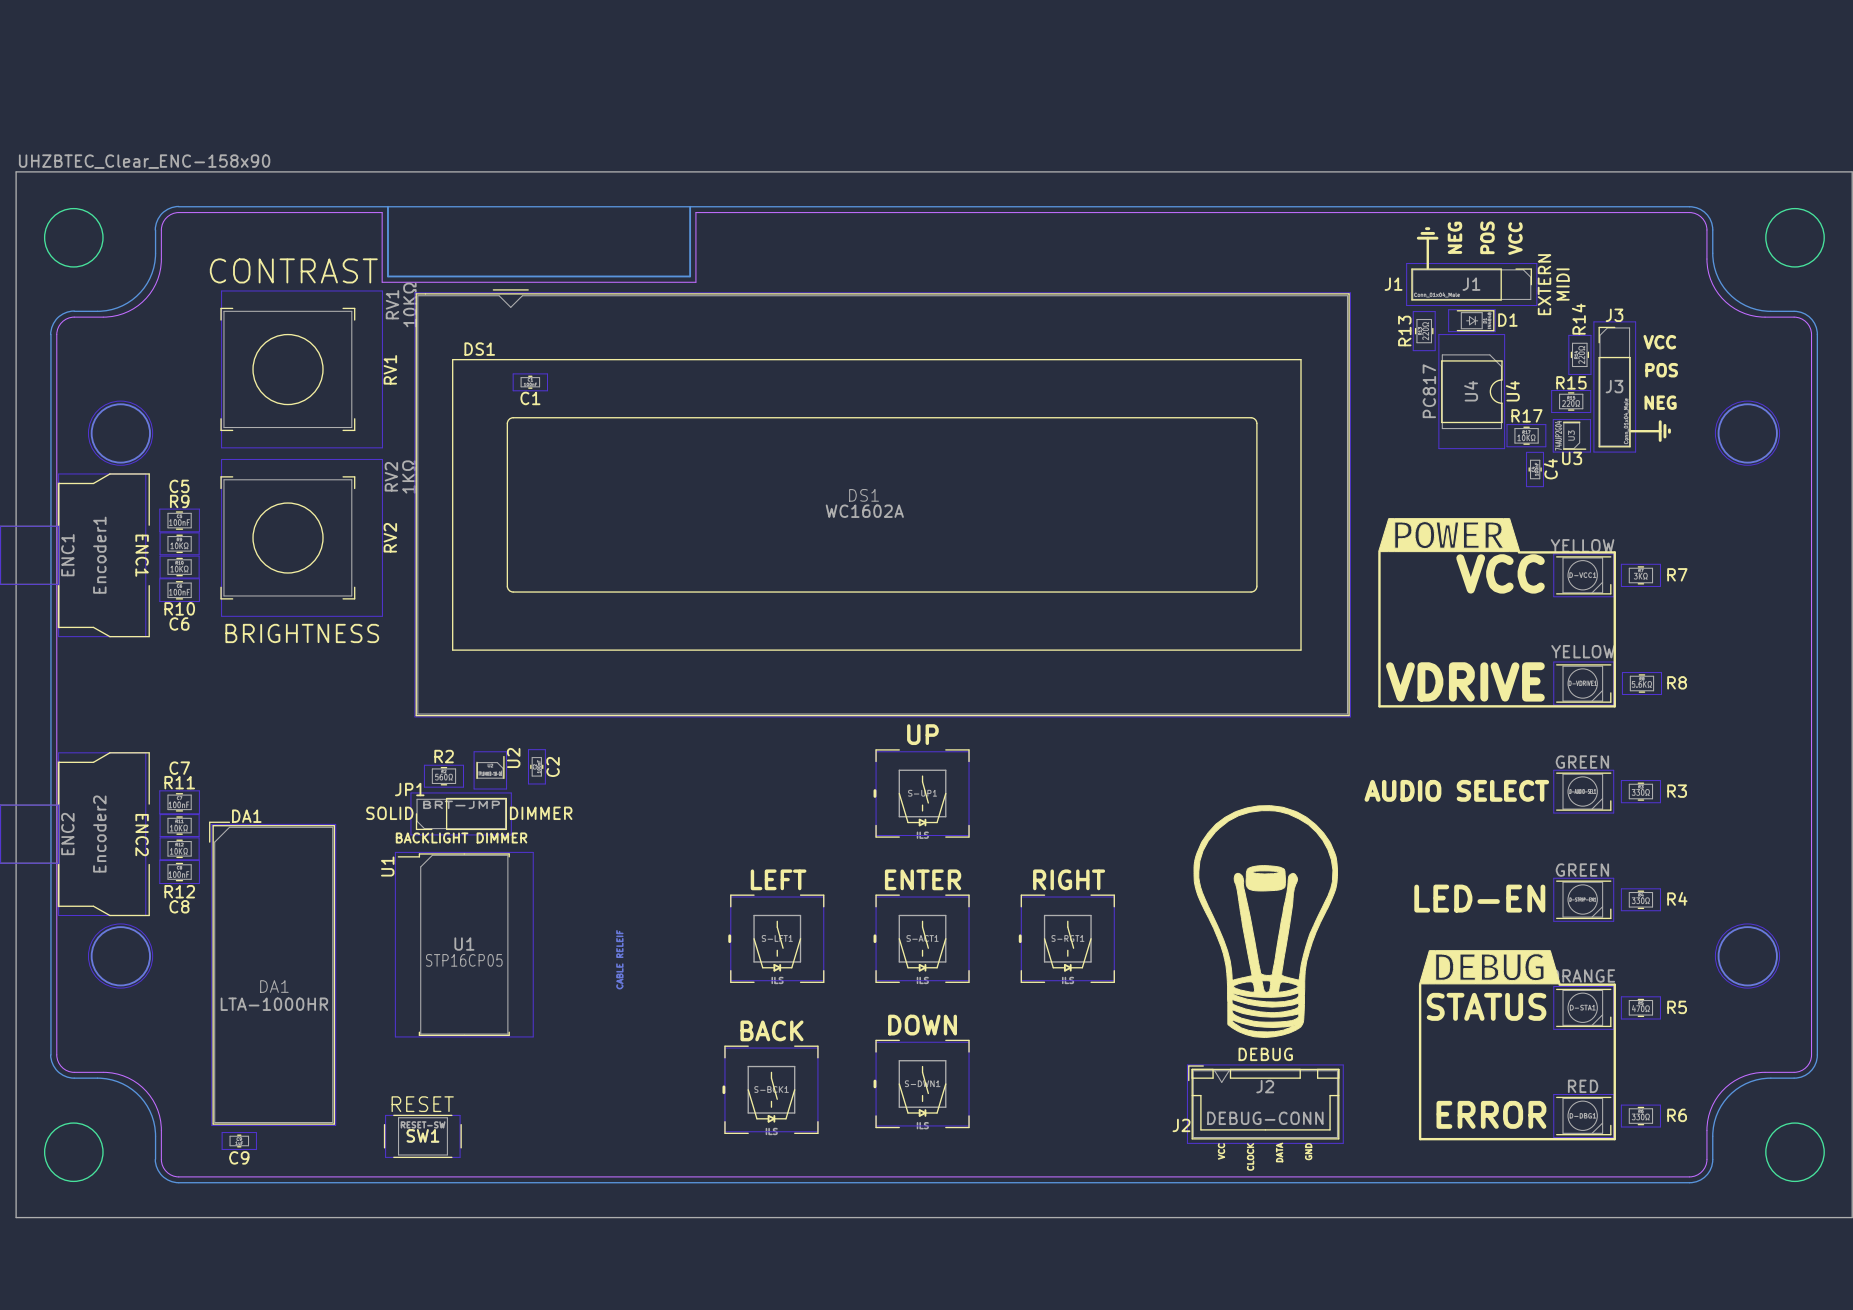
[picture p117: page 1]
