Daxxn/LightDrum/Docs/Schematics/REV7/Light-Drum-Interface-REV3-Comp-Bot.pdf

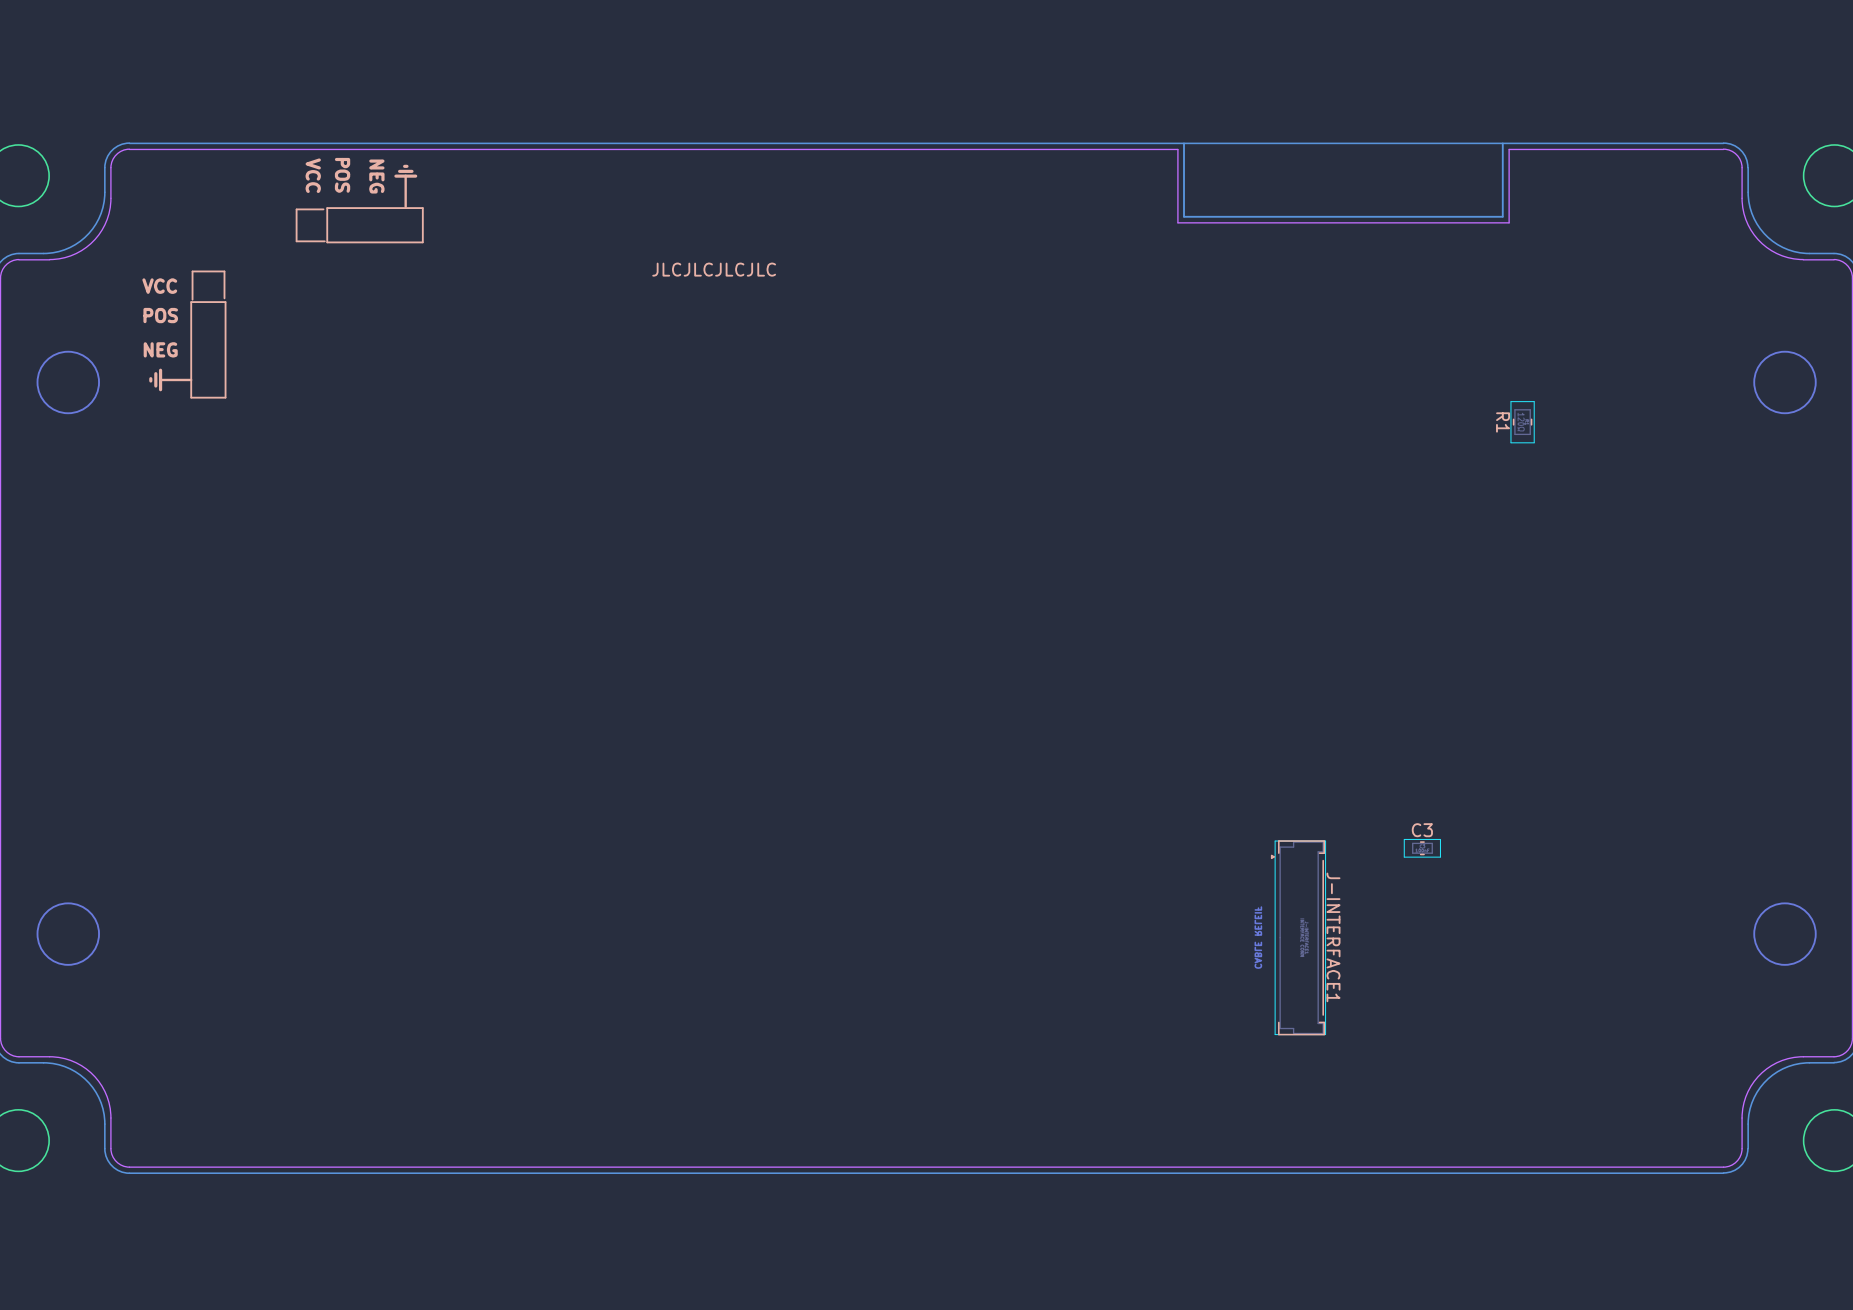
[picture p118: page 1]
