Daxxn/LightDrum/Docs/Schematics/REV7/Light-Drum-REV7-Comp-Bot.pdf

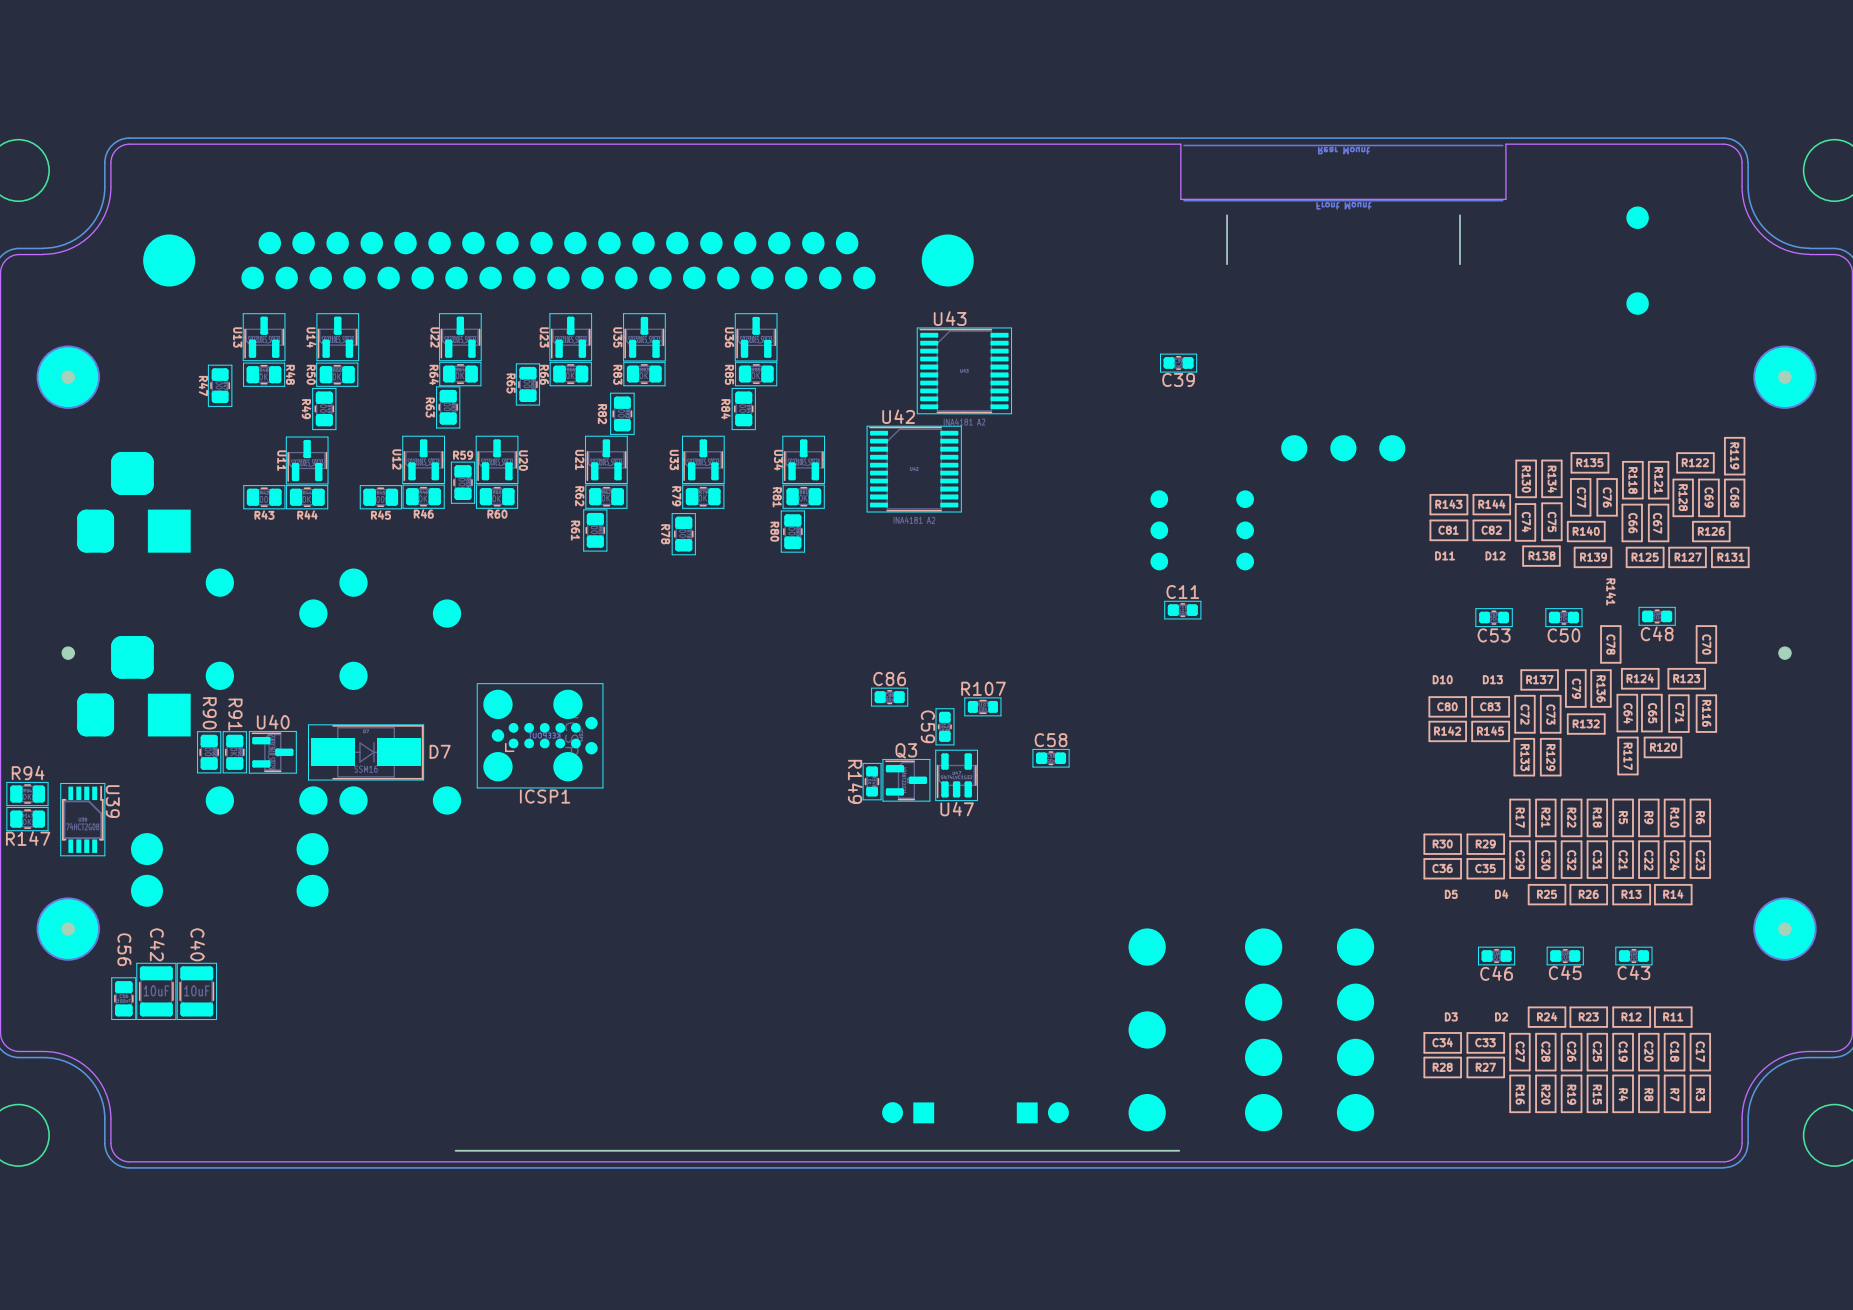
[picture p119: page 1]
