Daxxn/LightDrum/Docs/Schematics/REV7/Light-Drum-REV7-Comp-Top.pdf

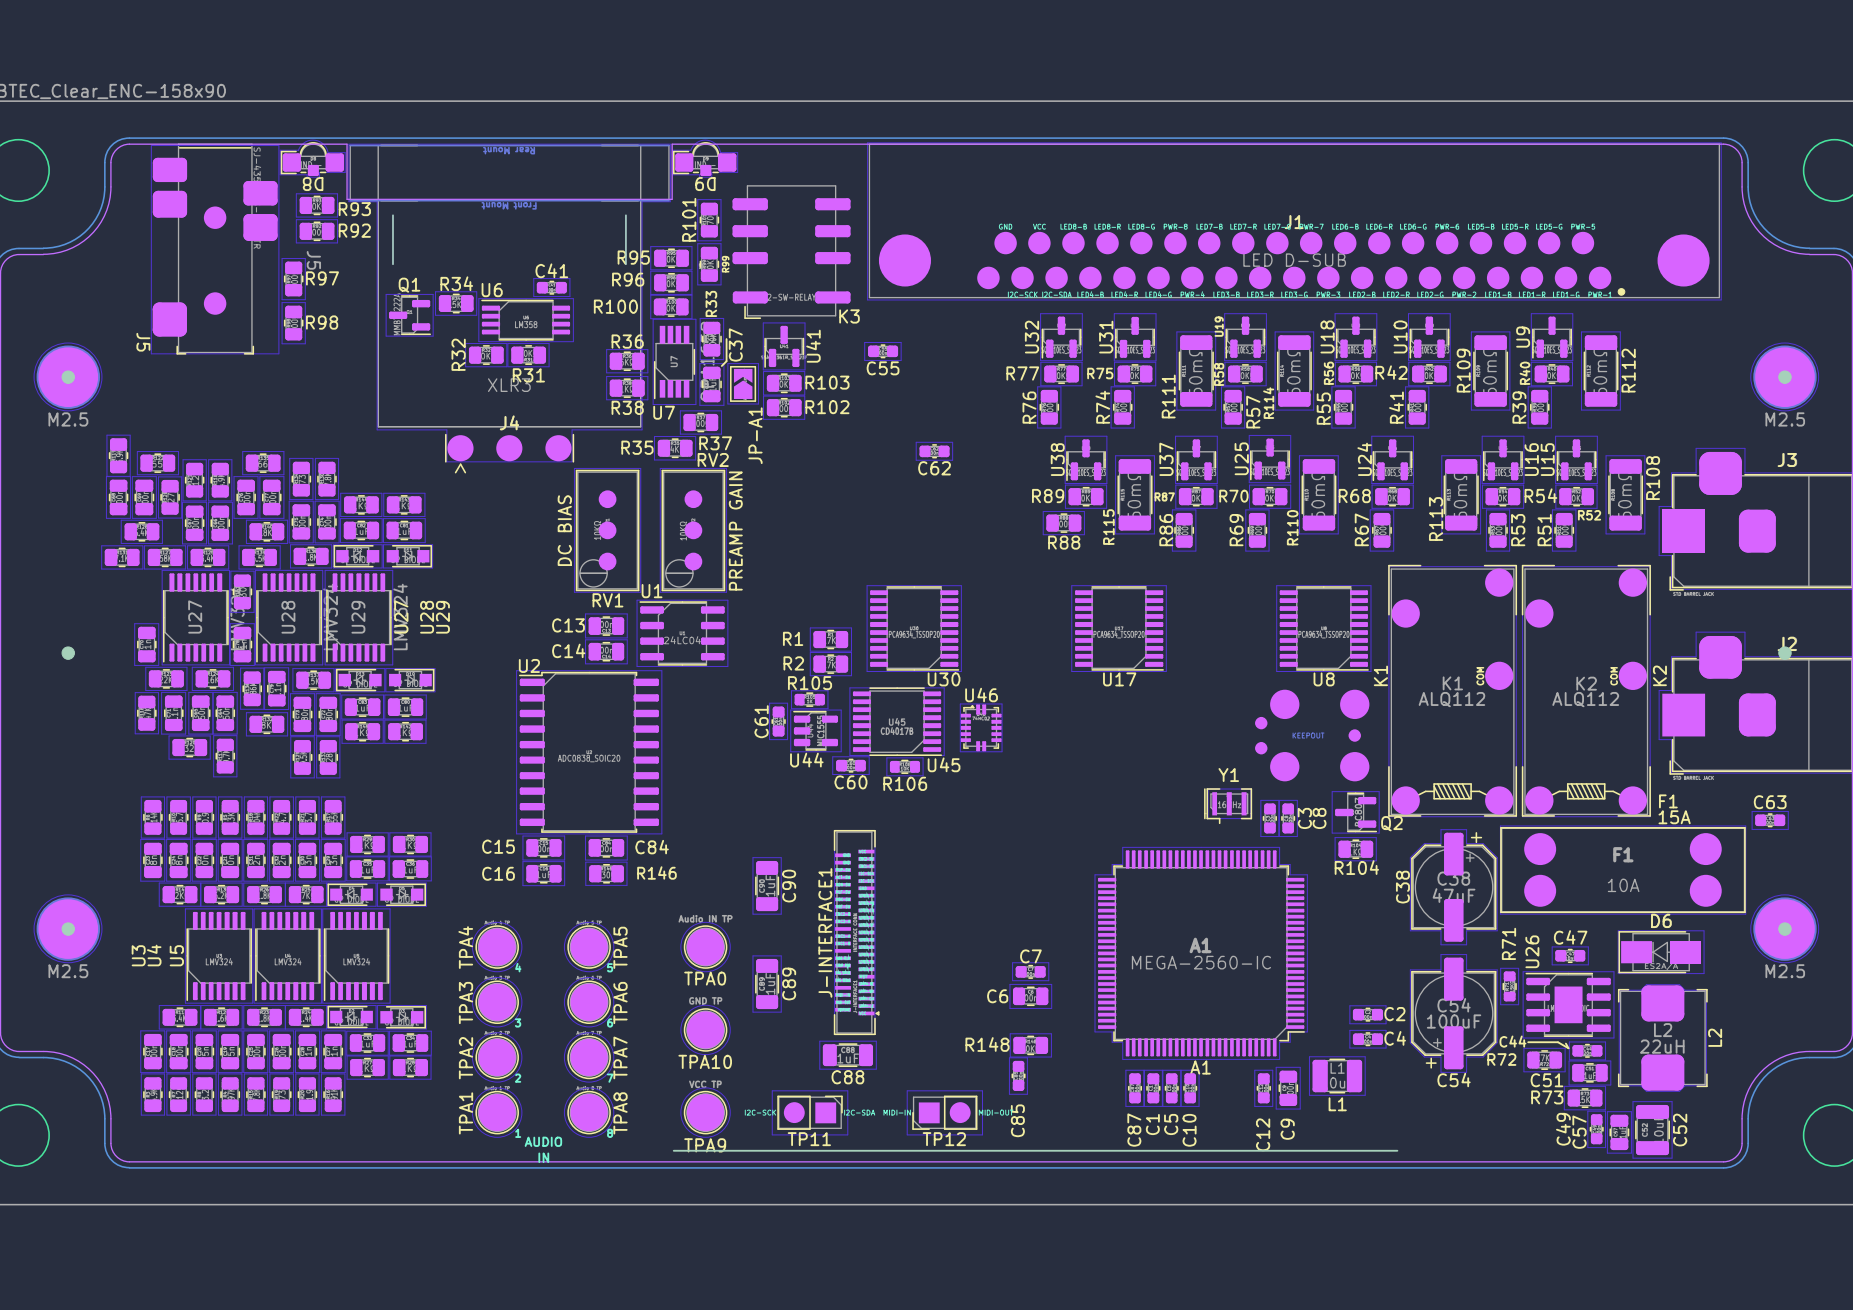
[picture p120: page 1]
