Daxxn/LightDrum/Docs/Schematics/REV5/InterfaceBoard-REV1-Bottom.pdf

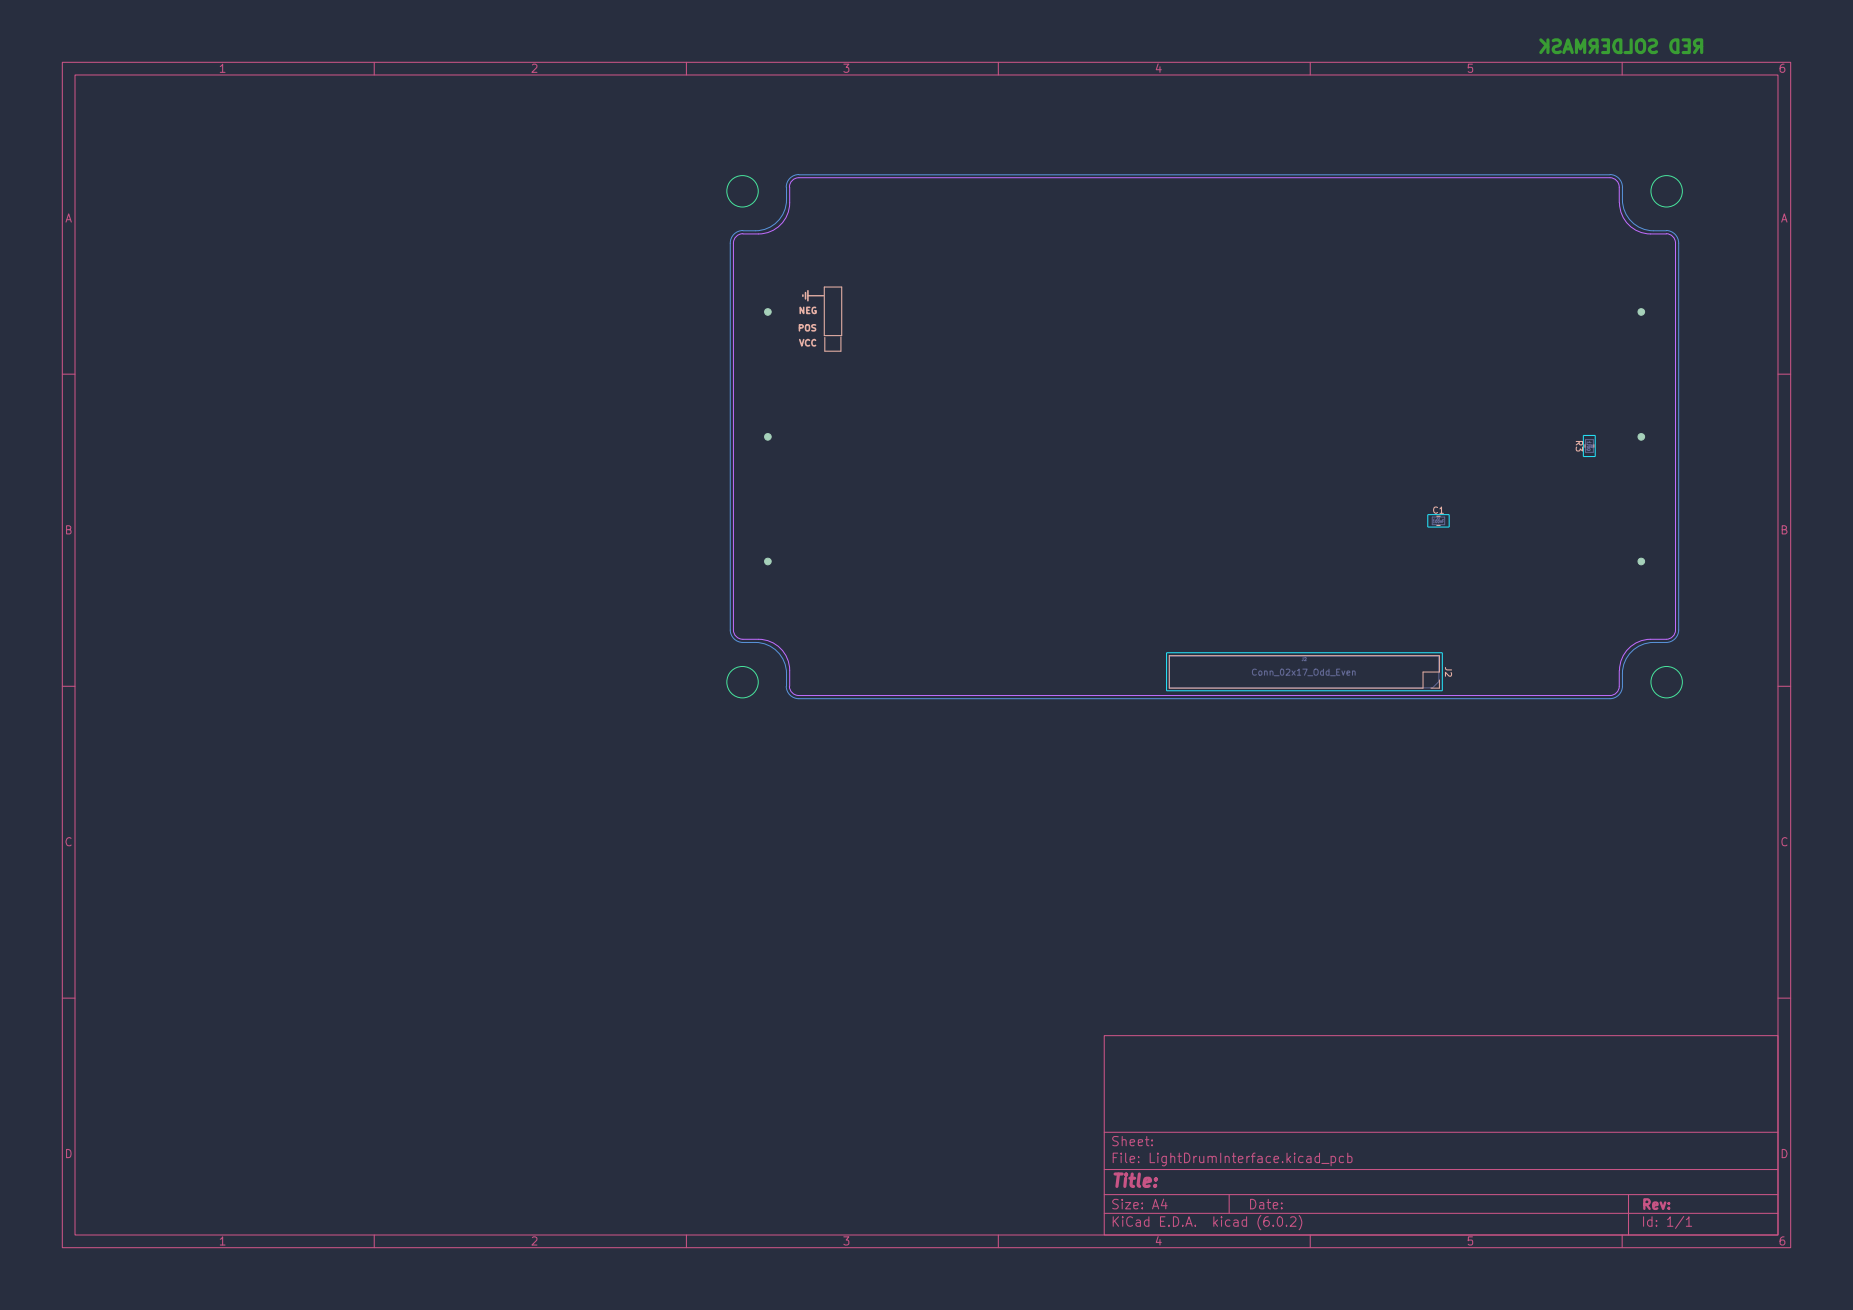
[picture p121: page 1]
