Daxxn/LightDrum/Docs/Schematics/REV5/InterfaceBoard-REV1-Top.pdf

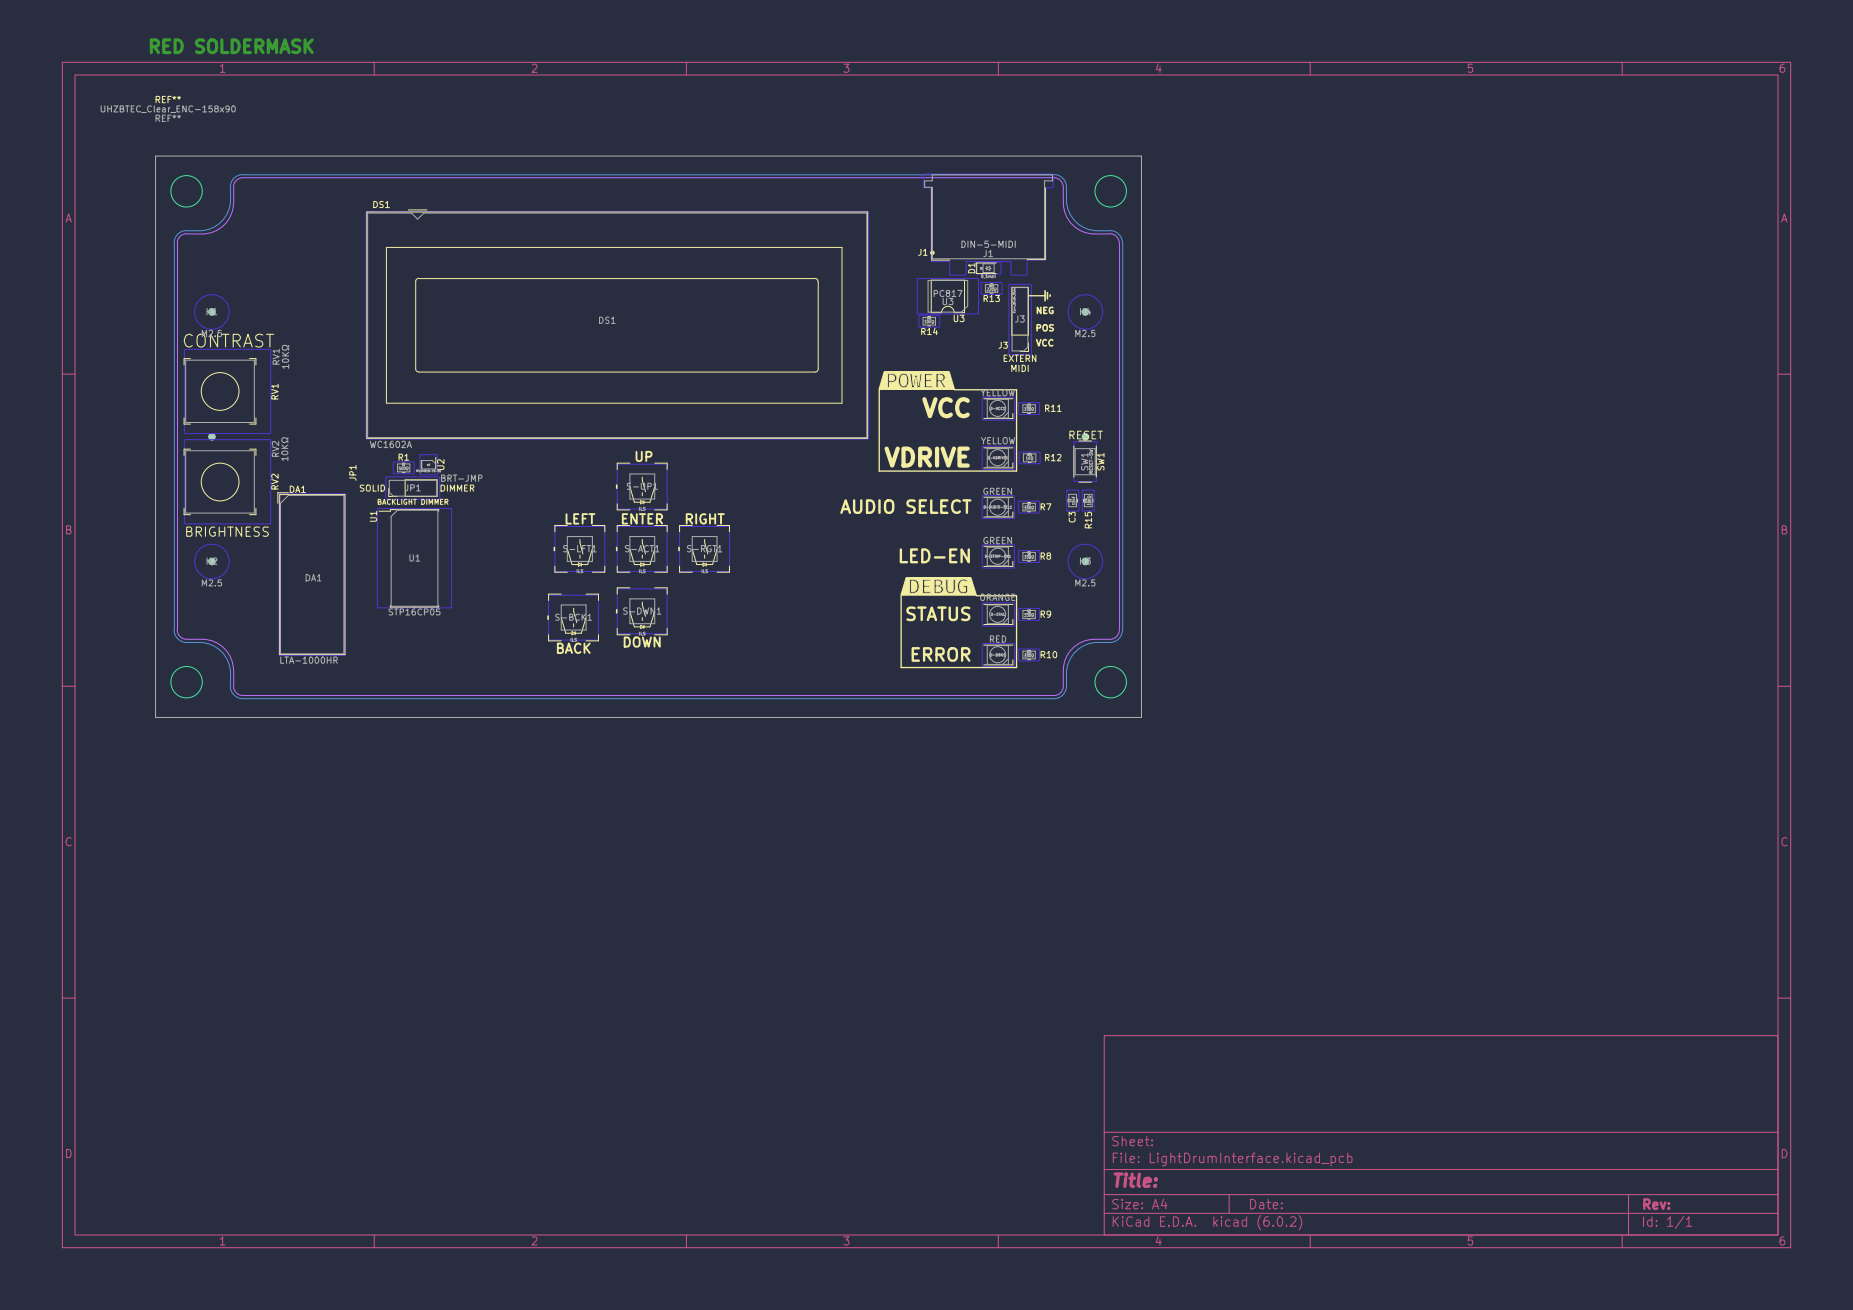
[picture p122: page 1]
