Daxxn/LightDrum/Docs/Schematics/REV5/MainBoard-REV5-Bottom.pdf

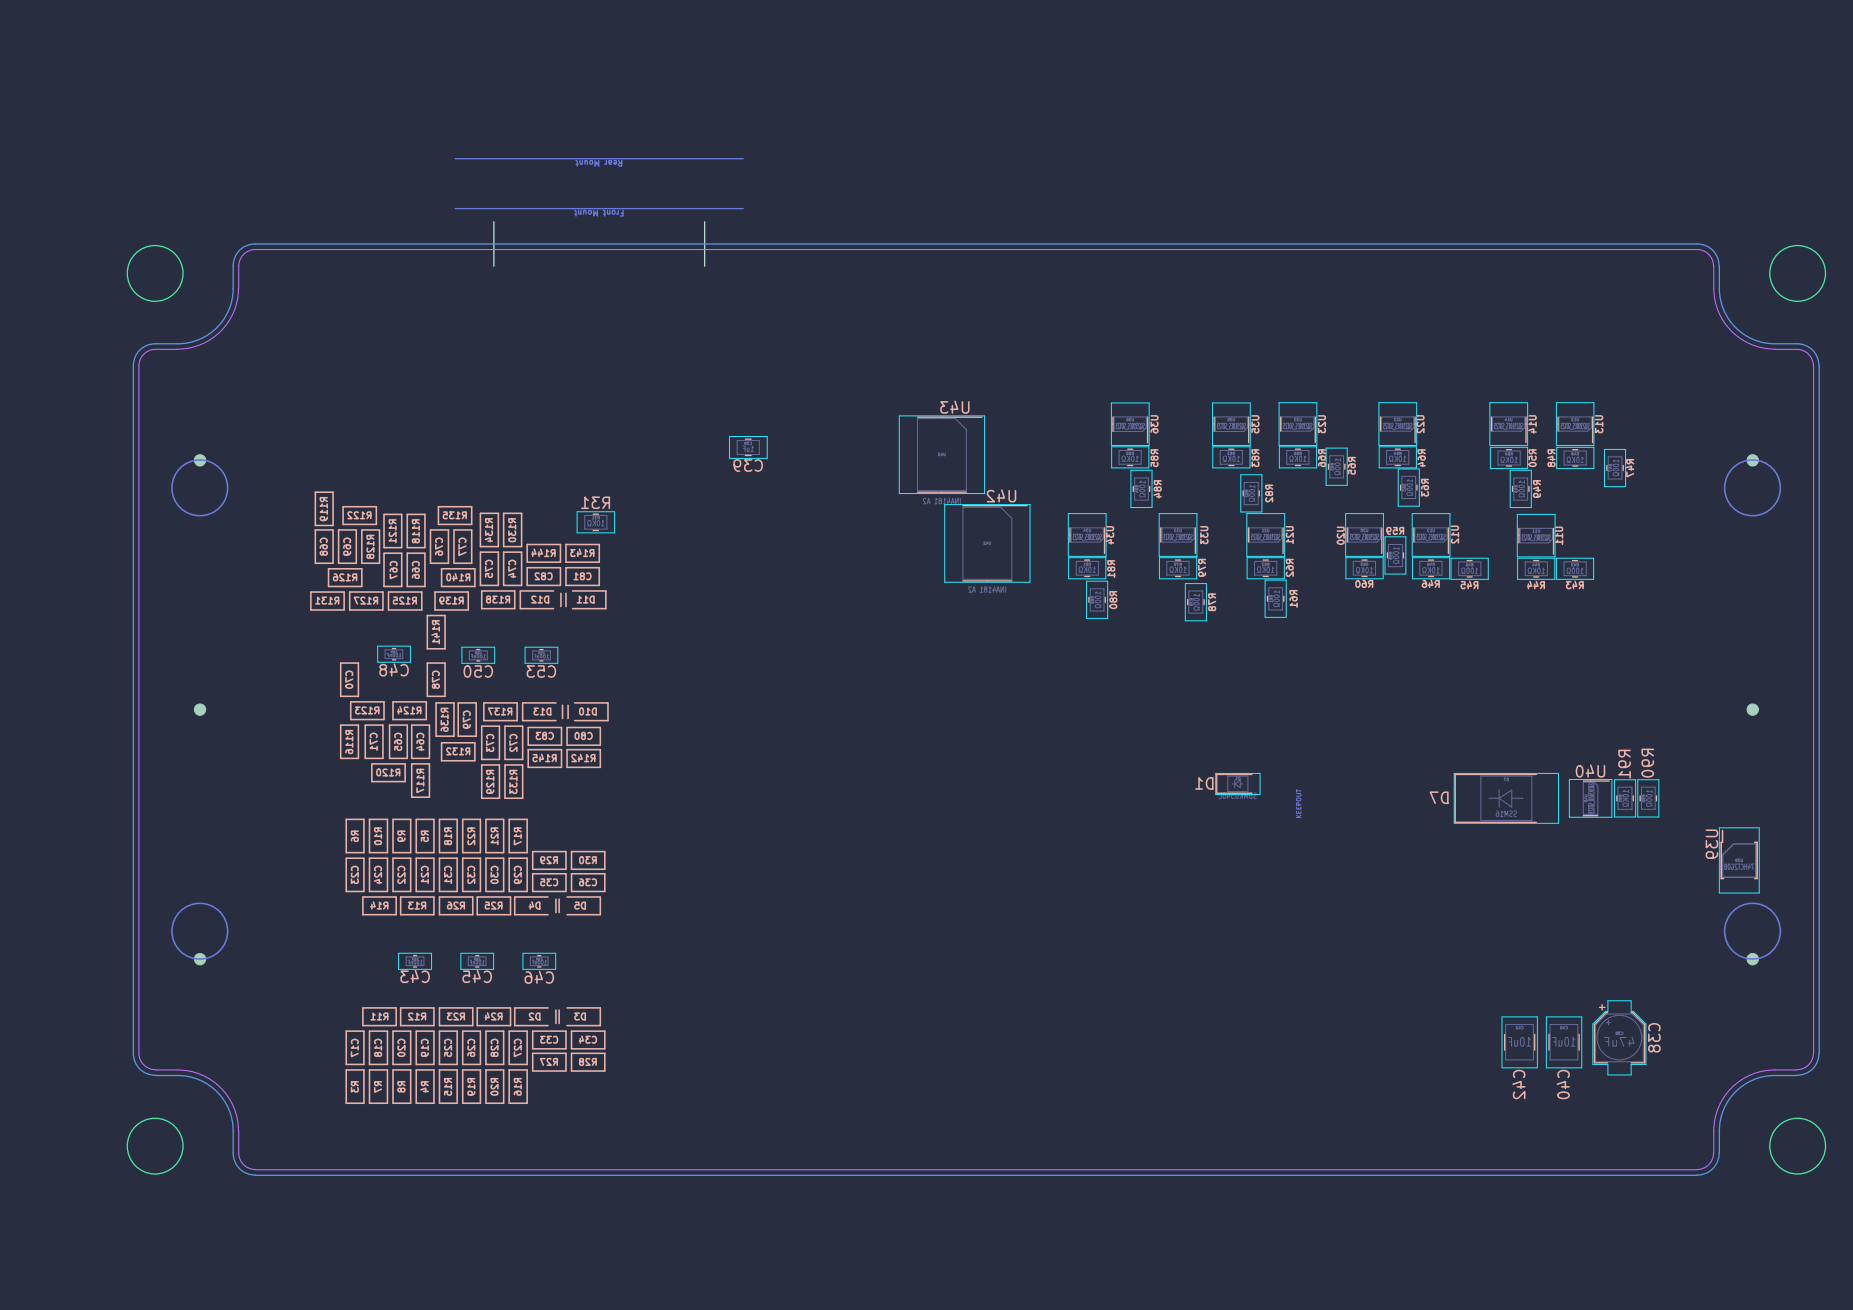
[picture p123: page 1]
