Daxxn/LightDrum/Docs/Schematics/REV5/MainBoard-REV5-Top.pdf

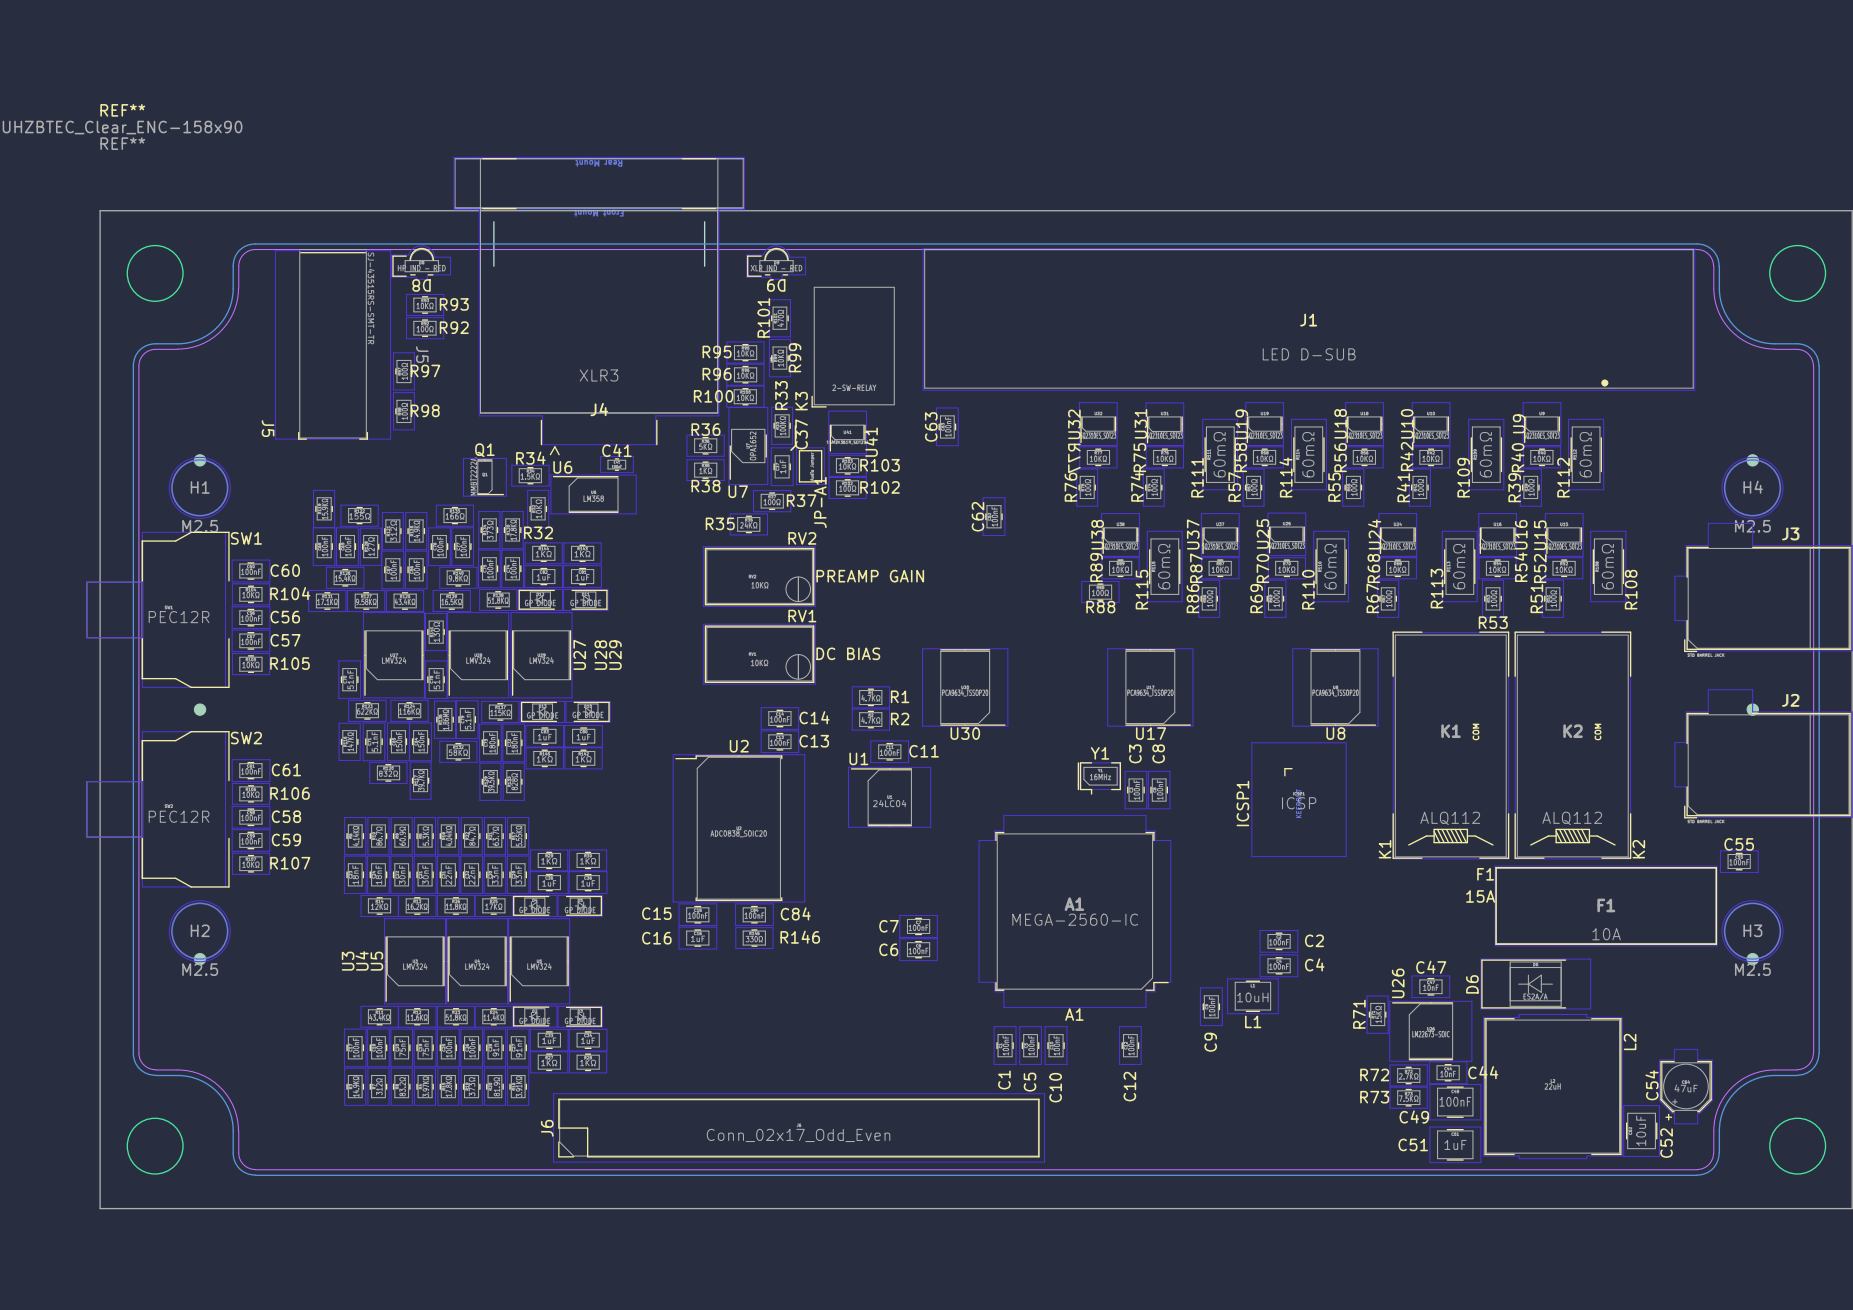
[picture p124: page 1]
