Daxxn/LightDrum/Docs/Schematics/REV5/LightDrum-Audiofilters-REV5-SCH.pdf

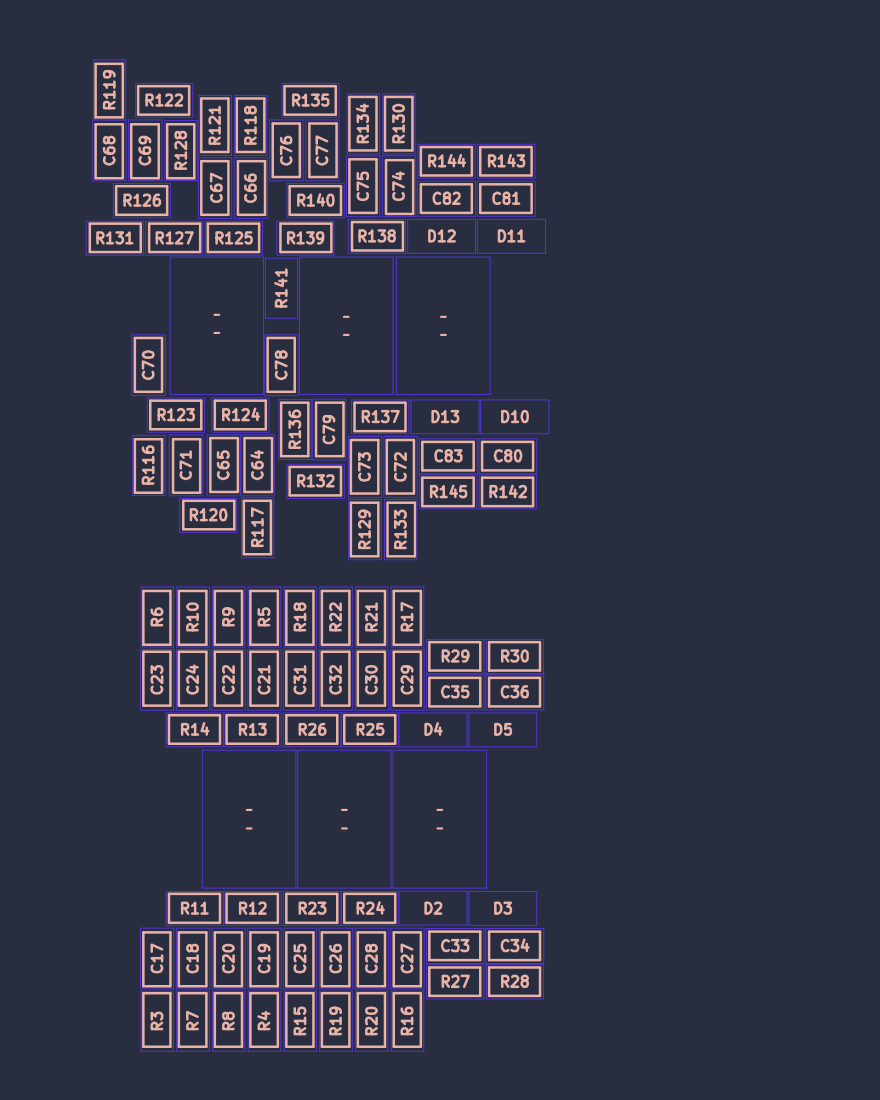
[picture p125: page 1]
