Daxxn/LightDrum/Docs/Schematics/REV5/LightDrum-Interface-REV1-SCH.pdf

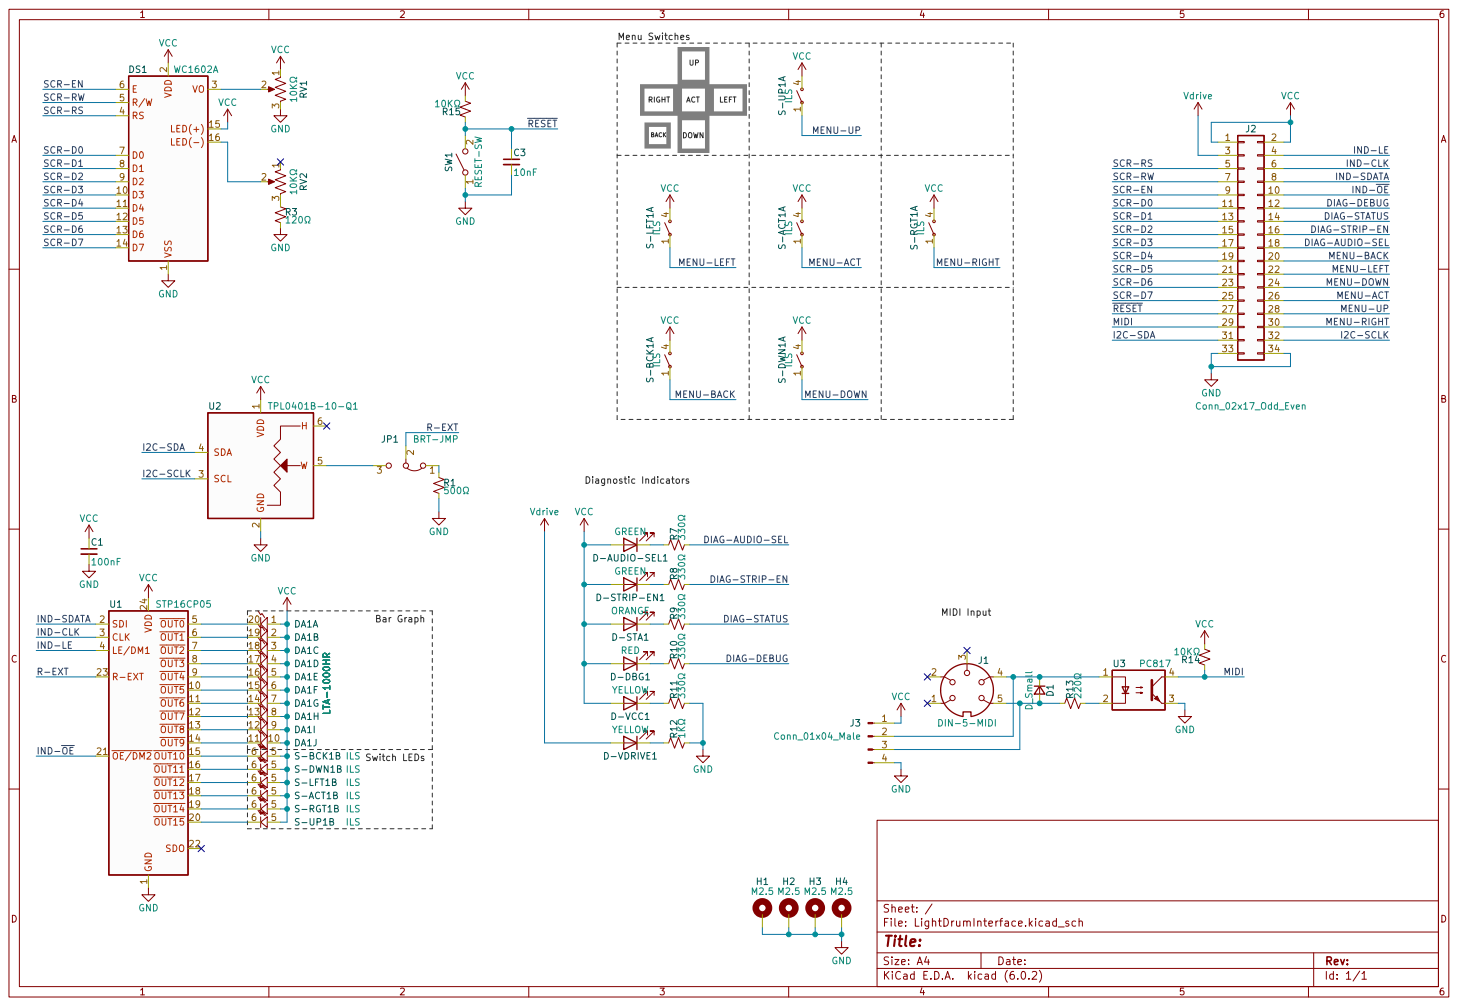
[picture p126: page 1]

VCC

SCR-D1 SCR-RW
~{RESET} R-EXT SCR-D3 SCR-D4 SCR-D0 SCR-RS

SCR-D1 SCR-D3 SCR-D6 SCR-D4 MENU-DOWN MENU-UP DIAG-STATUS DIAG-STRIP-EN

VCC | VCC | SCR-RS MENU-BACK MENU-LEFT

1 ~{OUT5}10 ~{OUT6}11 ~{OUT7}12 ~{OUT8}13 ~{OUT9}14 ~{OUT10}15 ~{OUT11}16 ~{OUT12}17 ~{OUT13}18 ~{OUT14}19 SDI 2 ~{OUT15}20 ~{OE/DM2} 21 SDO 22 R-EXT 23 VDD 24 CLK 3
IND-~{OE} R-EXT
