Daxxn/LightDrum/Docs/Schematics/REV6/Light-Drum-REV6-Comp-Bot.pdf

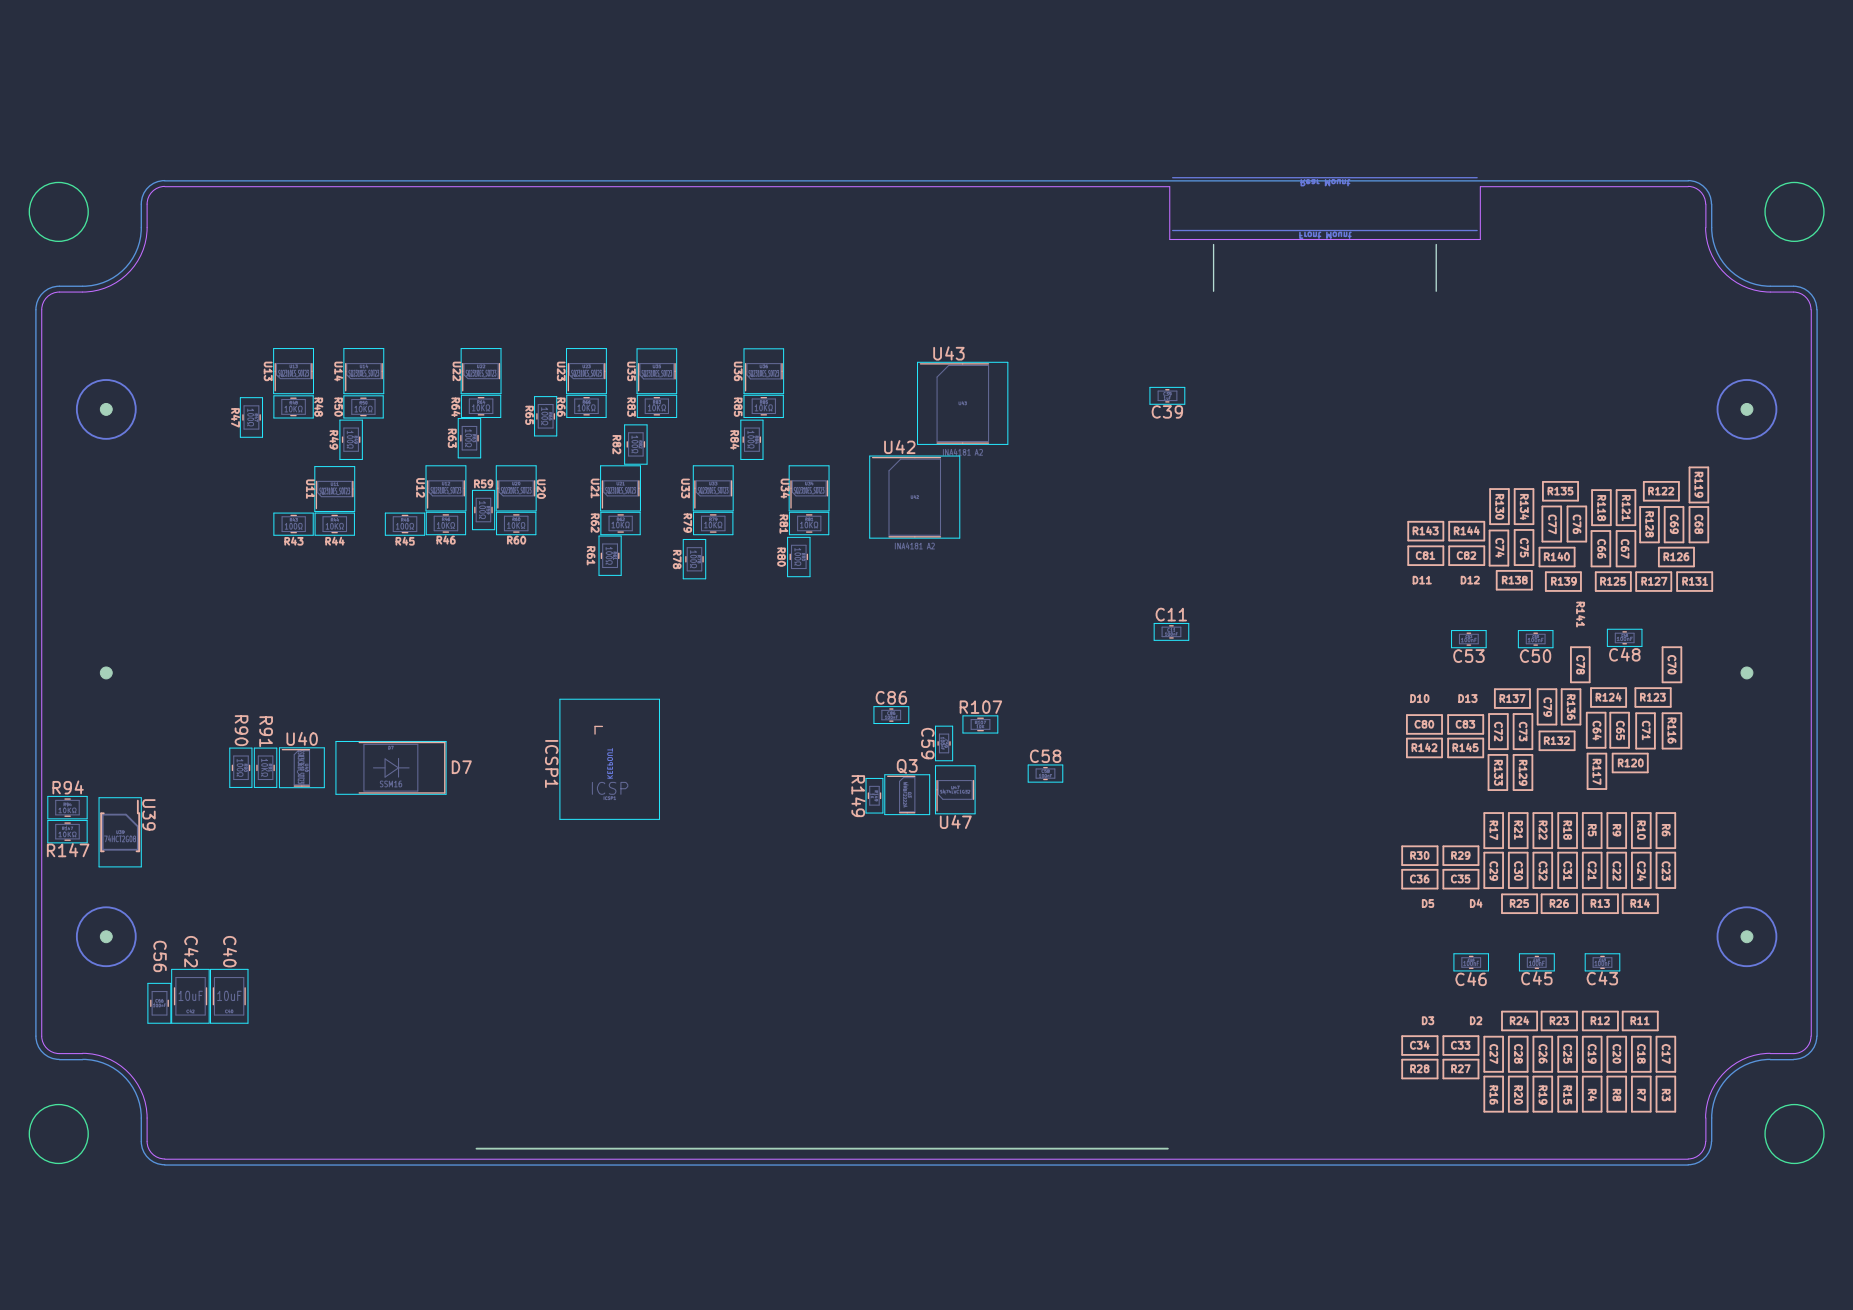
[picture p127: page 1]
