Daxxn/LightDrum/Docs/Schematics/REV6/Light-Drum-REV6-Comp-Top.pdf

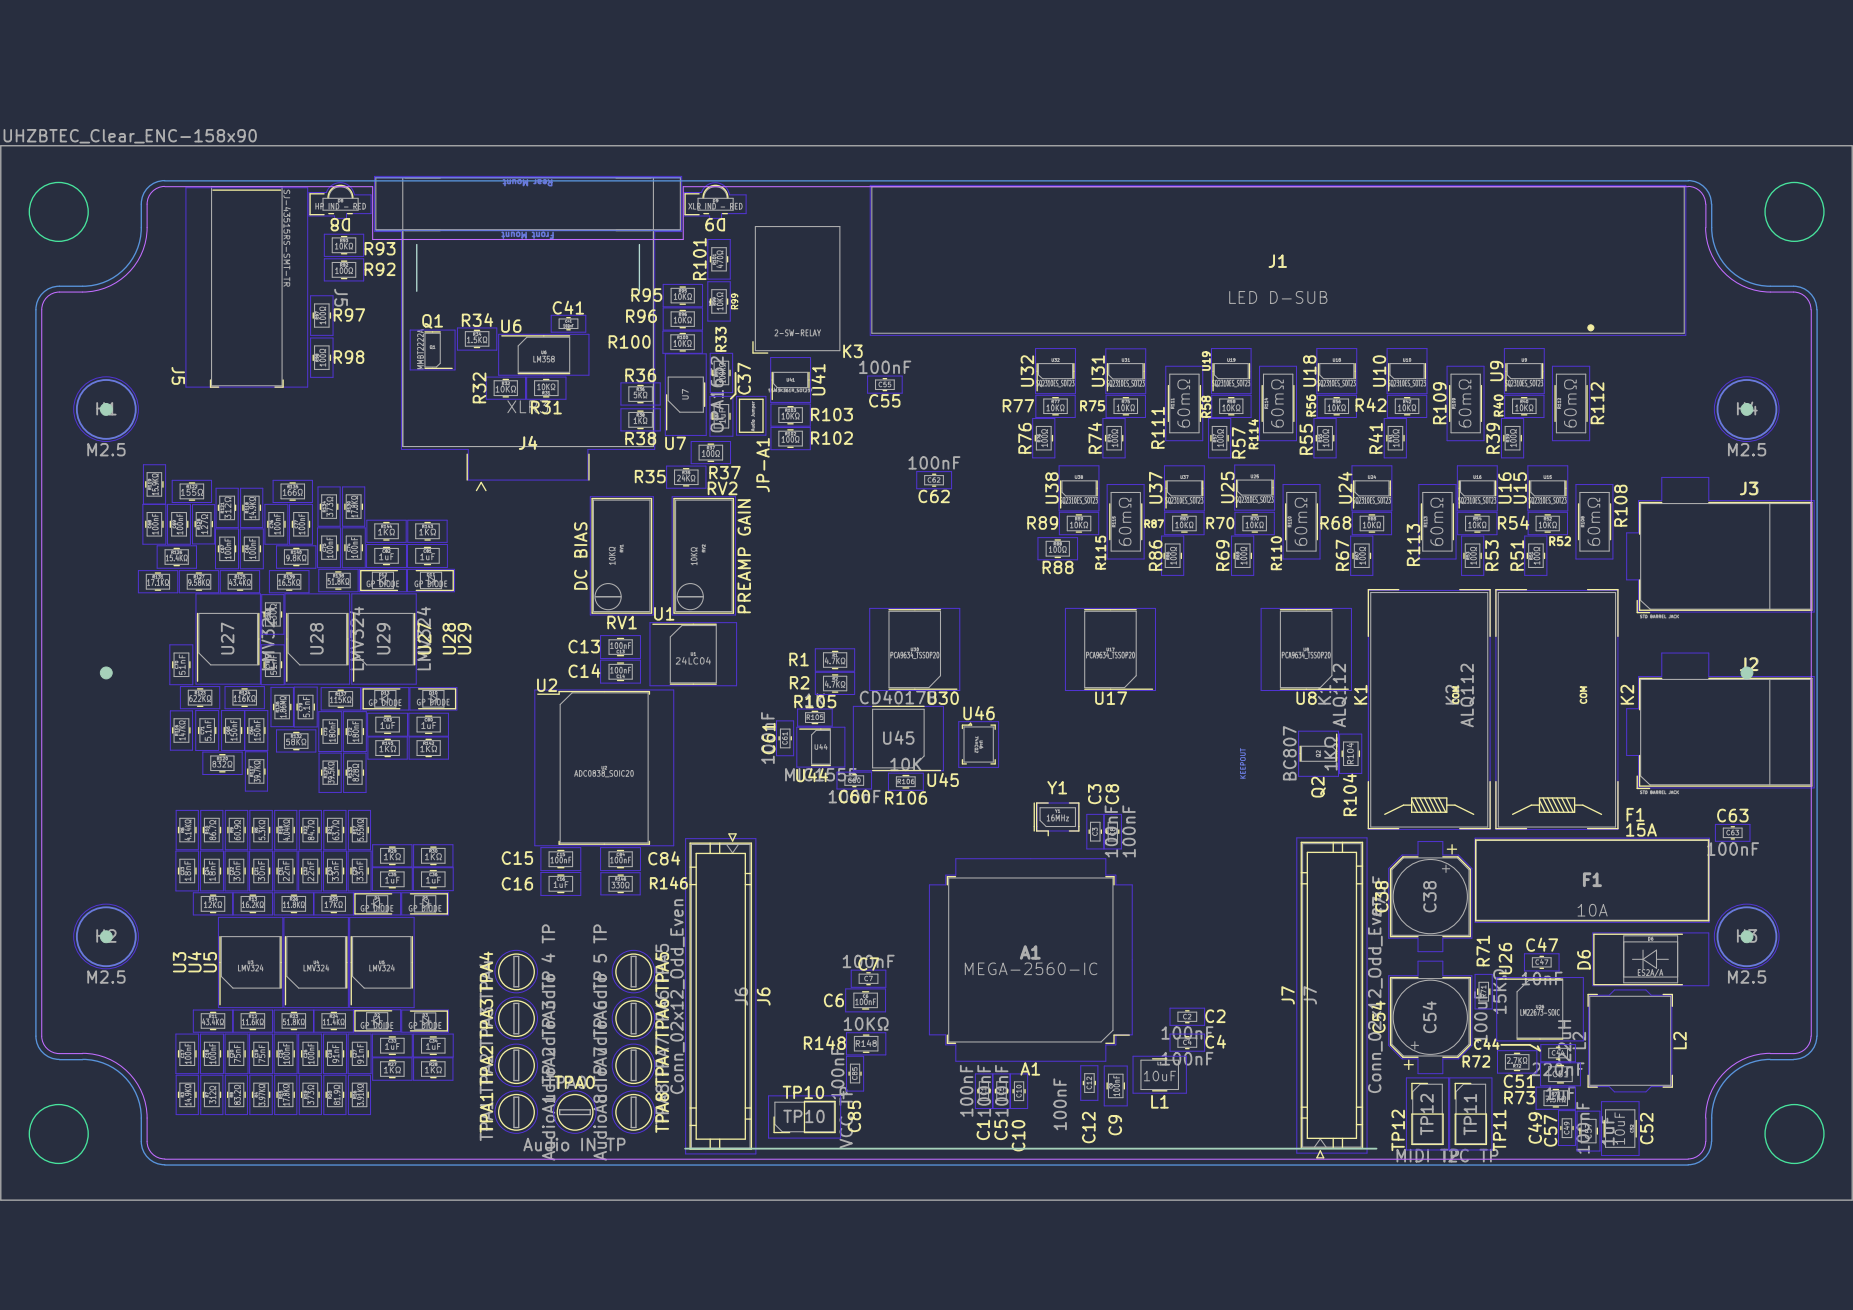
[picture p128: page 1]
