Daxxn/LightDrum/Docs/Schematics/REV6/Light-Drum-REV6-Conn.pdf

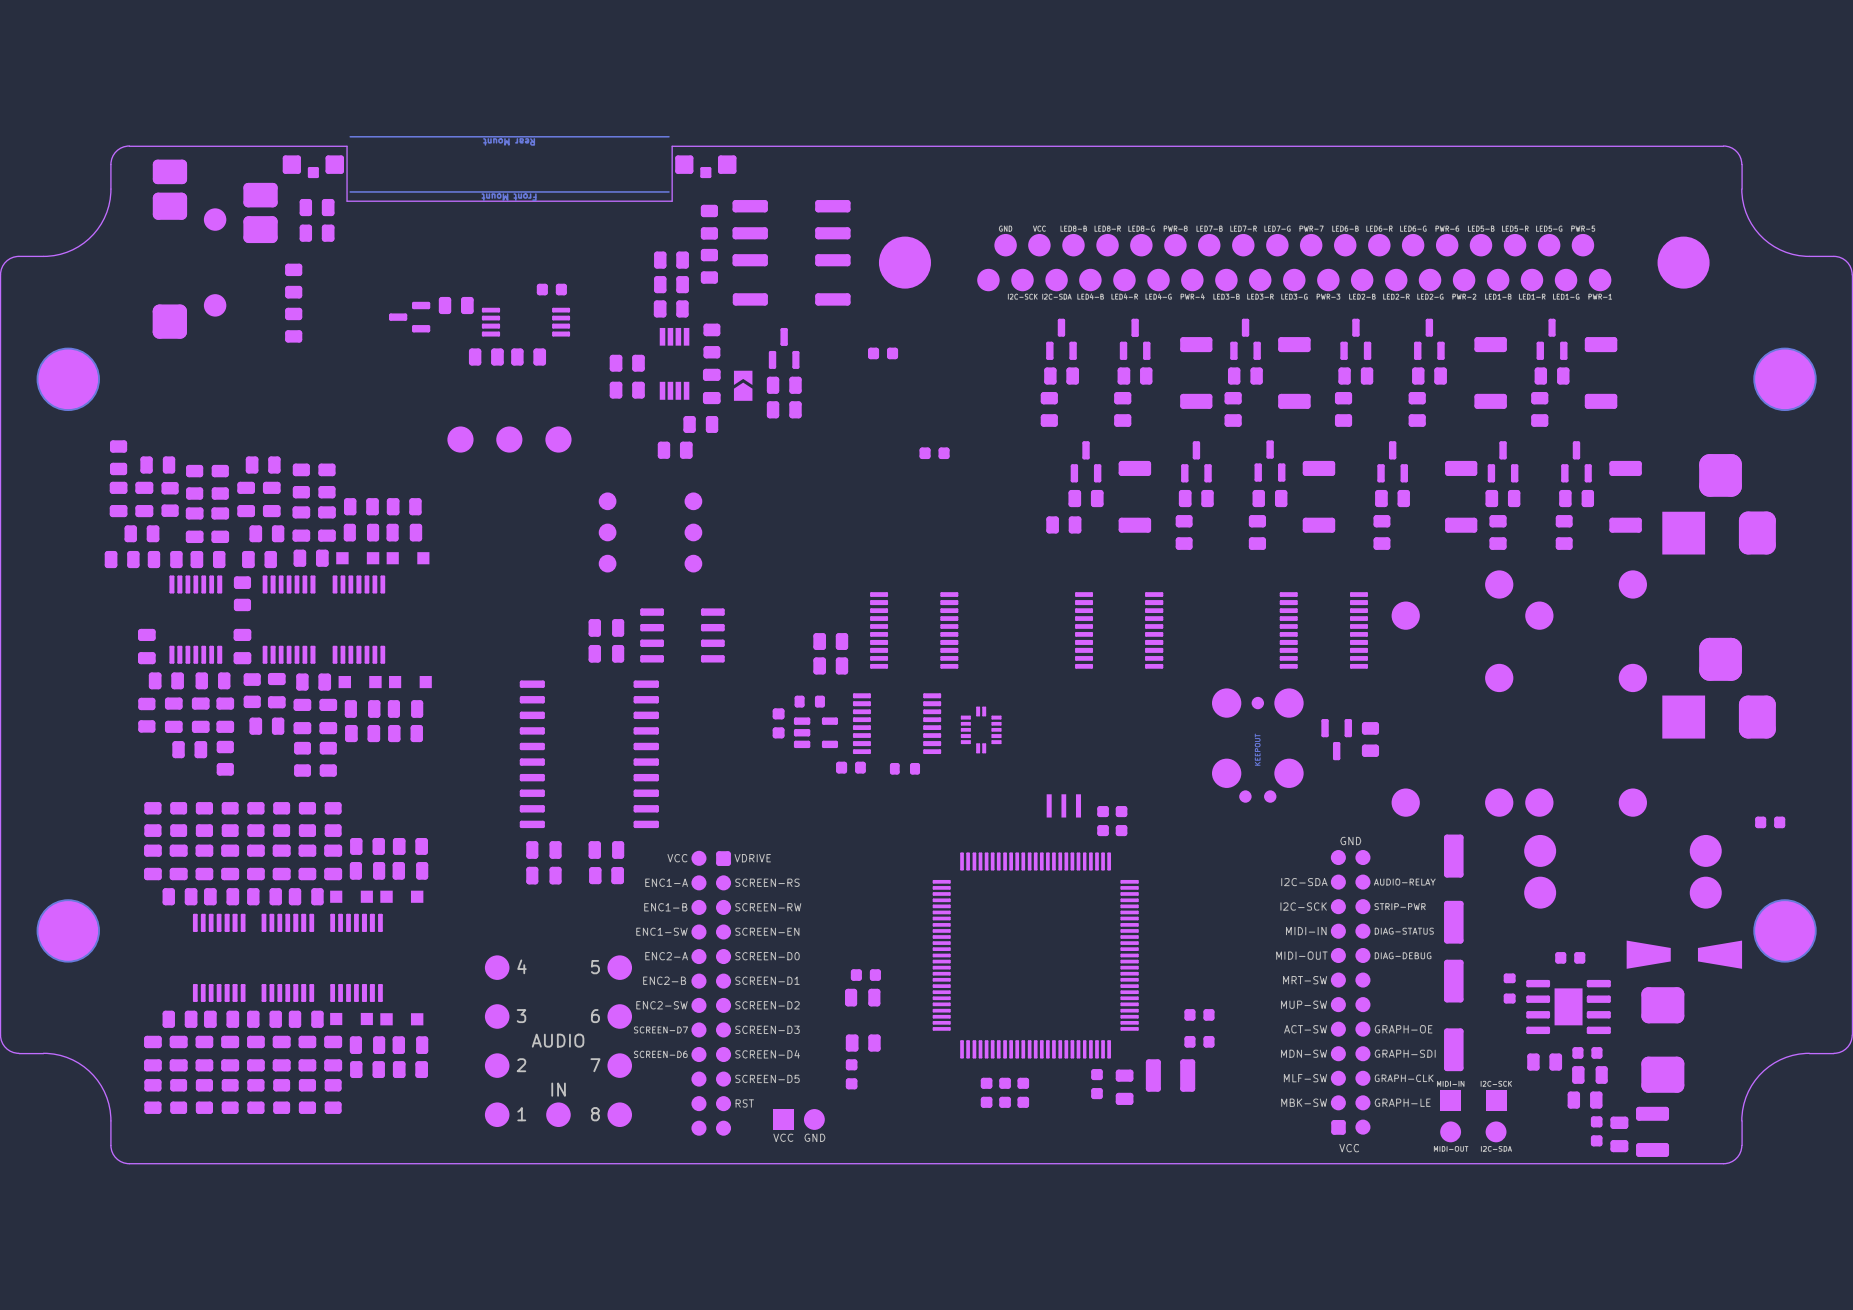
[picture p129: page 1]
