Daxxn/LightDrum/Docs/Schematics/PreviousRevisions/REV3/SpectrumFilterDTR-REV1-SCH.pdf

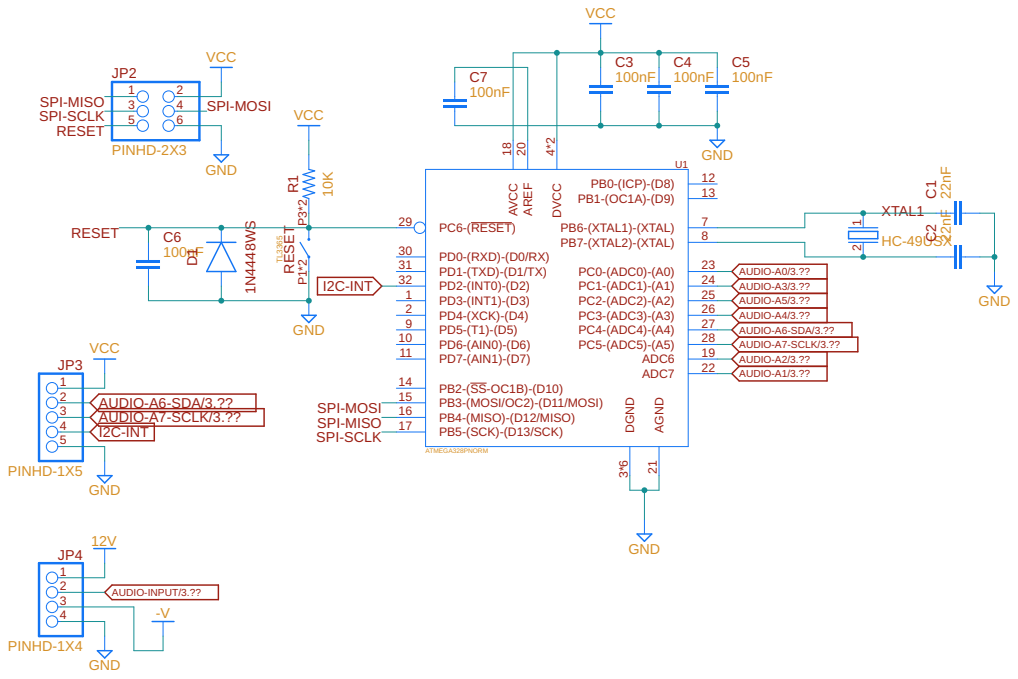
[picture p130: page 1]

AUDIO-A0/3.?? AUDIO-A3/3.?? AUDIO-A4/3.?? AUDIO-A2/3.?? AUDIO-A1/3.??

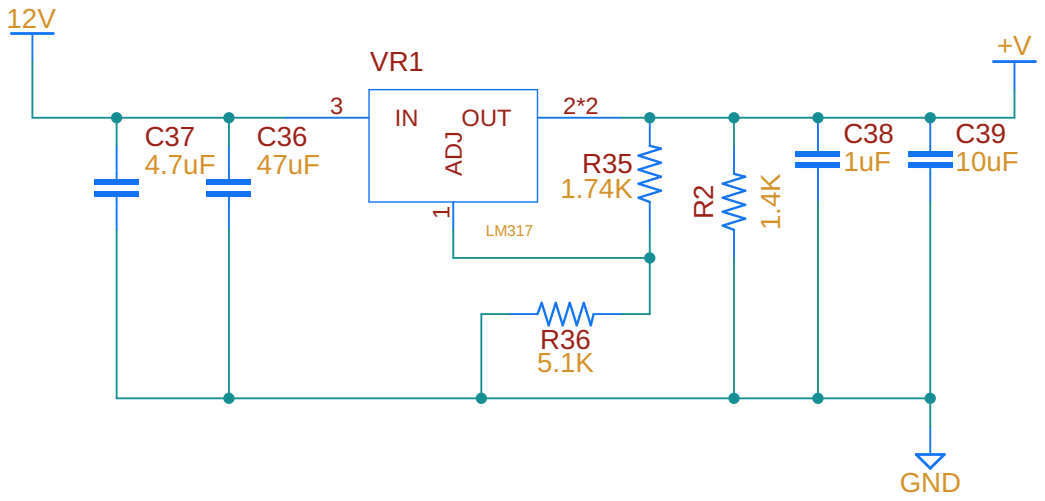
[picture p131: page 2]

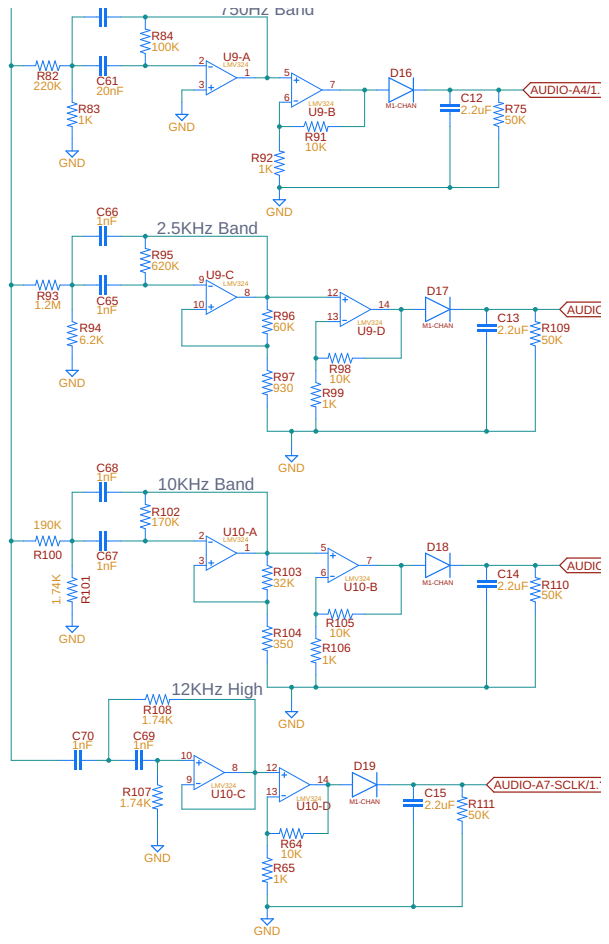
[picture p132: page 3]

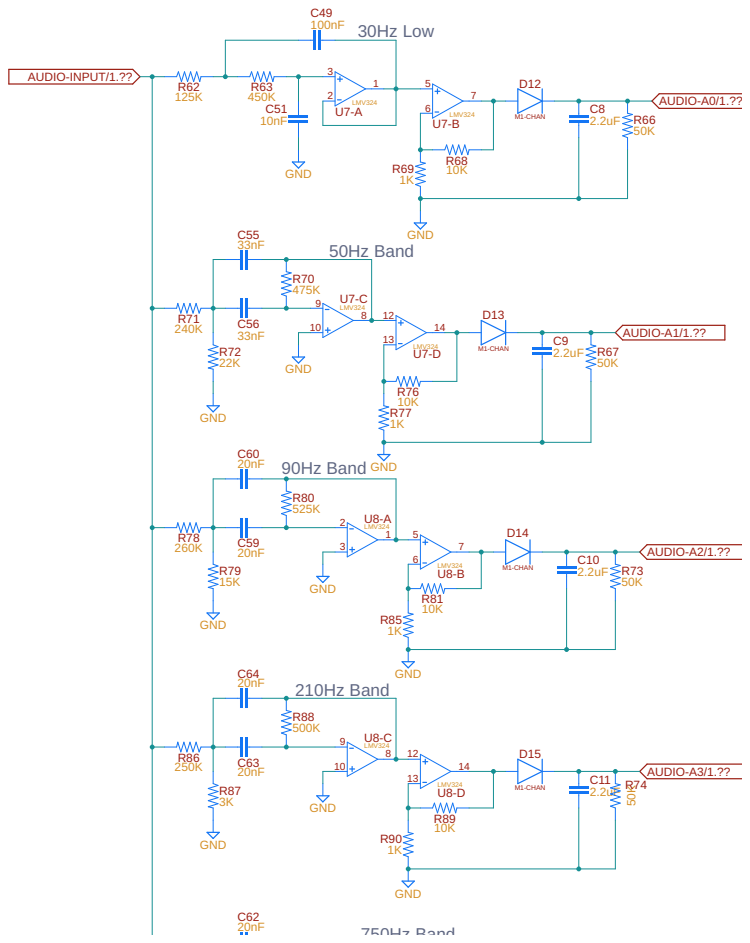
[picture p133: page 5]

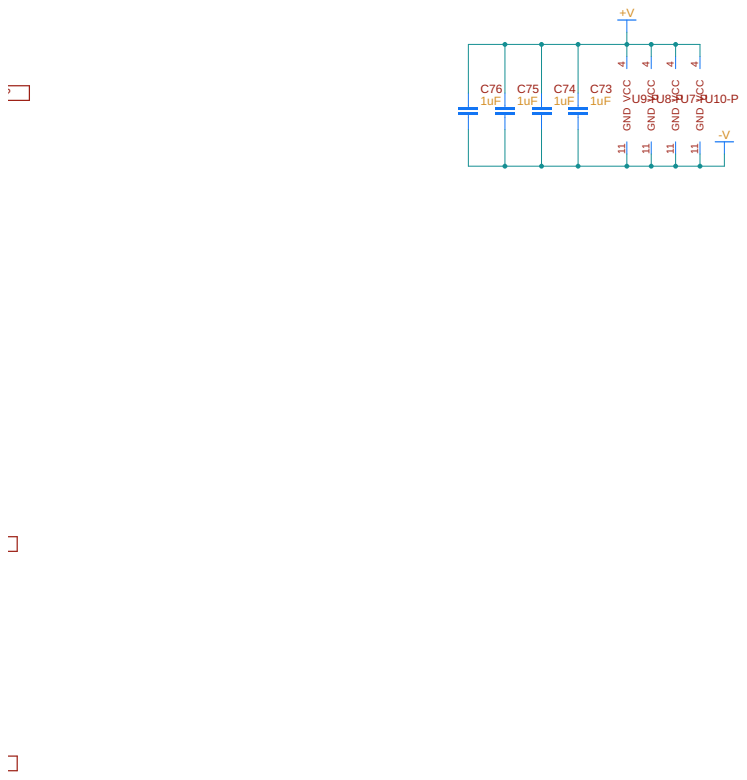
[picture p134: page 6]
