Daxxn/LightDrum/LightDrumFirmware/Cube/Core/Inc/main.h

#define GRAPH_CLK_Pin GPIO_PIN_2
#define GRAPH_CLK_GPIO_Port GPIOE
#define JACK_SW_Pin GPIO_PIN_3
#define JACK_SW_GPIO_Port GPIOE
#define GRAPH_SDI_Pin GPIO_PIN_6
#define GRAPH_SDI_GPIO_Port GPIOE
#define STRIP_ESHDN_Pin GPIO_PIN_0
#define STRIP_ESHDN_GPIO_Port GPIOC
#define VDD_PG_Pin GPIO_PIN_1
#define VDD_PG_GPIO_Port GPIOC
#define VAA_PG_Pin GPIO_PIN_2
#define VAA_PG_GPIO_Port GPIOC
#define STRIP_PG_Pin GPIO_PIN_3
#define STRIP_PG_GPIO_Port GPIOC
#define SOLID_LGTS_MON_Pin GPIO_PIN_0
#define SOLID_LGTS_MON_GPIO_Port GPIOA
#define MIDI_OUT_Pin GPIO_PIN_2
#define MIDI_OUT_GPIO_Port GPIOA
#define MIDI_IN_Pin GPIO_PIN_3
#define MIDI_IN_GPIO_Port GPIOA
#define STRIP_MON2_Pin GPIO_PIN_4
#define STRIP_MON2_GPIO_Port GPIOA
#define STRIP_MON1_Pin GPIO_PIN_5
#define STRIP_MON1_GPIO_Port GPIOA
#define STRIP_MON6_Pin GPIO_PIN_6
#define STRIP_MON6_GPIO_Port GPIOA
#define STRIP_MON5_Pin GPIO_PIN_7
#define STRIP_MON5_GPIO_Port GPIOA
#define STRIP_MON4_Pin GPIO_PIN_4
#define STRIP_MON4_GPIO_Port GPIOC
#define STRIP_MON3_Pin GPIO_PIN_5
#define STRIP_MON3_GPIO_Port GPIOC
#define STRIP_MON8_Pin GPIO_PIN_0
#define STRIP_MON8_GPIO_Port GPIOB
#define STRIP_MON7_Pin GPIO_PIN_1
#define STRIP_MON7_GPIO_Port GPIOB
#define XLR_SEL_IND_Pin GPIO_PIN_9
#define XLR_SEL_IND_GPIO_Port GPIOE
#define HP_SEL_IND_Pin GPIO_PIN_13
#define HP_SEL_IND_GPIO_Port GPIOE
#define MENU_LEFT_Pin GPIO_PIN_15
#define MENU_LEFT_GPIO_Port GPIOE
#define MENU_LEFT_EXTI_IRQn EXTI15_10_IRQn
#define DMX_TX_Pin GPIO_PIN_10
#define DMX_TX_GPIO_Port GPIOB
#define ENC2_B_Pin GPIO_PIN_12
#define ENC2_B_GPIO_Port GPIOB
#define ENC2_A_Pin GPIO_PIN_13
#define ENC2_A_GPIO_Port GPIOB
#define ENC2_A_EXTI_IRQn EXTI15_10_IRQn
#define ENC1_A_Pin GPIO_PIN_14
#define ENC1_A_GPIO_Port GPIOB
#define ENC1_A_EXTI_IRQn EXTI15_10_IRQn
#define ENC2_SW_Pin GPIO_PIN_8
#define ENC2_SW_GPIO_Port GPIOD
#define ENC2_SW_EXTI_IRQn EXTI9_5_IRQn
#define MENU_RIGHT_Pin GPIO_PIN_9
#define MENU_RIGHT_GPIO_Port GPIOD
#define MENU_RIGHT_EXTI_IRQn EXTI9_5_IRQn
#define MENU_ACT_Pin GPIO_PIN_10
#define MENU_ACT_GPIO_Port GPIOD
#define MENU_ACT_EXTI_IRQn EXTI15_10_IRQn
#define MENU_BACK_Pin GPIO_PIN_11
#define MENU_BACK_GPIO_Port GPIOD
#define MENU_BACK_EXTI_IRQn EXTI15_10_IRQn
#define MENU_UP_Pin GPIO_PIN_12
#define MENU_UP_GPIO_Port GPIOD
#define MENU_UP_EXTI_IRQn EXTI15_10_IRQn
#define ENC1_B_Pin GPIO_PIN_13
#define ENC1_B_GPIO_Port GPIOD
#define GRAPH_LE_Pin GPIO_PIN_14
#define GRAPH_LE_GPIO_Port GPIOD
#define GRAPH_OE_Pin GPIO_PIN_15
#define GRAPH_OE_GPIO_Port GPIOD
#define PWM_OE_Pin GPIO_PIN_6
#define PWM_OE_GPIO_Port GPIOC
#define DIAG_DEBUG_Pin GPIO_PIN_8
#define DIAG_DEBUG_GPIO_Port GPIOC
#define DIAG_STATUS_Pin GPIO_PIN_9
#define DIAG_STATUS_GPIO_Port GPIOC
#define SCREEN_TX_Pin GPIO_PIN_9
#define SCREEN_TX_GPIO_Port GPIOA
#define SCREEN_RX_Pin GPIO_PIN_10
#define SCREEN_RX_GPIO_Port GPIOA
#define DMX_EN_Pin GPIO_PIN_10
#define DMX_EN_GPIO_Port GPIOC
#define DMX_RX_Pin GPIO_PIN_11
#define DMX_RX_GPIO_Port GPIOC
#define STRIP_PWR_Pin GPIO_PIN_0
#define STRIP_PWR_GPIO_Port GPIOD
#define SDIO_CD_Pin GPIO_PIN_1
#define SDIO_CD_GPIO_Port GPIOD
#define MENU_DOWN_Pin GPIO_PIN_3
#define MENU_DOWN_GPIO_Port GPIOD
#define MENU_DOWN_EXTI_IRQn EXTI3_IRQn
#define ENC1_SW_Pin GPIO_PIN_5
#define ENC1_SW_GPIO_Port GPIOD
#define ENC1_SW_EXTI_IRQn EXTI9_5_IRQn
#define LGT_EN3_Pin GPIO_PIN_9
#define LGT_EN3_GPIO_Port GPIOB
#define LGT_EN2_Pin GPIO_PIN_0
#define LGT_EN2_GPIO_Port GPIOE
#define LGT_EN1_Pin GPIO_PIN_1
#define LGT_EN1_GPIO_Port GPIOE
#define FMPI2C_TIMEOUT 200
#define STRIP_CHANNEL_SIZE 8
#define UINT32_HALF 2147483647
#define UINT16_HALF 32767
#define UINT8_HALF  127
#define MENU_DEBOUNCE_WAIT 1
